alxgmpr/moisture-sensor/docs/footprint-standardization-2026-09-09/README.md

# Standard KiCad footprints — 9 September 2026

Implemented the requested corrections in the maintained PCB and schematic.

- All 11 resistors use `Resistor_SMD:R_0402_1005Metric`.
- Nine 0402 capacitors use `Capacitor_SMD:C_0402_1005Metric`; C3 retains the standard 0603 pattern.
- Corrected C21/C22/C23/C24/C27 pad rotation by loading standard library geometry. Replaced C26 and R22/R23/R36/R37 hand-solder geometry with standard reflow geometry and moved 12 attached track endpoints to the new pad centers.
- D1–D10 now use `Package_SON:Texas_DPY0002A_0.6x1mm_P0.65mm`. Its pad dimensions and centers match the former custom pattern. The installed library's referenced STEP model is missing, so the existing local matching DPY model is retained; copper, mask, paste, courtyard, silk and fabrication geometry come from KiCad.
- Other ICs already select standard KiCad footprints. Retained the verified custom module, battery holder, crystal and inductor patterns because matching part-specific entries were not found in the installed standard library.
- Preserved every footprint placement, purchased part number, pad-to-net assignment, via, and keepout. The user confirmed the no-via corridor is intended for GND vias only; the two existing +3V3 keepout errors are accepted for this change. Rules and exclusions were not edited.
- Updated HARDWARE.md and LAYOUT.md to the selected Lian Xin CR2032-BS-6/C22363833 holder, corrected C22/C24 to 0402 X7R/50 V, and corrected the holder-model entry in NEXT-STEPS.md.
- Regenerated [product-bom.csv](product-bom.csv) using KiCad's schematic exporter, then regenerated the BOM.md table from that CSV. Purchasing MPNs are unchanged.

## Validation

[Geometry and preservation checks](verification.json) confirm all 31 updated footprints have the standard library's pad numbers, positions, orientation, size, shape, corner ratio and copper/mask/paste layers. No HandSolder footprint remains in the maintained PCB or schematic.

[Final DRC](drc.json): zero unconnected items, zero schematic parity differences, and only the two user-accepted +3V3 keepout errors. There are 39 warnings: 35 silk/text, two existing IC-library differences, one dangling track and one dangling via. Some silk overlaps result from retaining unmodified standard footprint silk. No additional electrical DRC error was introduced.

[ERC](erc.json): zero errors and 11 warnings (ten symbol/library differences and one connected no-connect warning).

[Full existing test suite](tests.txt): 49 tests, 46 pass, three fail. Re-running the suite with PCB/schematic/project reads redirected to the saved pre-change files reproduces the same three failures; [baseline comparison](baseline-tests.txt). The failures concern the outdated model-less test-point inventory, a D8 ground-via proximity expectation, and the existing SENSE track-width setting. No new test failure remains. The subprocess-based export checks use the maintained schematic in both runs; the three failing tests read the snapshotted source directly.

Inspected the updated [top view](top.png), component closeups, and KiCad layer exports in [layers](layers/). Available models show no new obvious component collision. The new standard pads remain connected after zone refill and trace-end adjustment.

The [preceding review](../footprint-review-2026-09-09/README.md) records the pre-change findings. Its recommendation concerning the two +3V3 vias is superseded by the user's explicit clarification above. Existing fabrication ZIPs/Gerbers were not regenerated by this footprint update; generate production output from the corrected sources before ordering.
