alxgmpr/moisture-sensor/output/front-graphic-concepts/prompts-botanical.md

# Botanical variants

Created with the built-in image generator, editing mono-v2.png.

## sunflower

Edit the supplied black-and-white pixel-art plant emblem. Preserve the existing pot, bottom two leaves, curved stem base, three radio wave arcs at upper right, black and white palette, square canvas, and overall scale. Replace ONLY the carnivorous head and its upper attachment with the requested non-carnivorous plant top. No teeth, jaws, mouth, eyes, face, spikes or carnivorous features. A charming botanical radio-broadcasting emblem, waves visually radiate from the new plant top. Bold crisp stair-stepped square pixel edges, simple chunky shapes, high readability on a small device. Solid black and pure white only. No gray, textures, shading, text, additional objects or borders. Replace head with a single round sunflower with a bold black central disk, small white center detail, and a ring of about eight broad blocky petals separated by white notches. Flower tilts subtly toward the radio arcs. Keep flower compact and silhouette unmistakable.

## sprout

Edit the supplied black-and-white pixel-art plant emblem. Preserve the existing pot, bottom two leaves, curved stem base, three radio wave arcs at upper right, black and white palette, square canvas, and overall scale. Replace ONLY the carnivorous head and its upper attachment with the requested non-carnivorous plant top. No teeth, jaws, mouth, eyes, face, spikes or carnivorous features. A charming botanical radio-broadcasting emblem, waves visually radiate from the new plant top. Bold crisp stair-stepped square pixel edges, simple chunky shapes, high readability on a small device. Solid black and pure white only. No gray, textures, shading, text, additional objects or borders. Replace head with a botanical leafy shoot: upper curved stem ending in three broad smooth oval pixel leaves, one top leaf and two alternating side leaves, each with a simple white central vein. Healthy ordinary houseplant, no flower, no face. Leaves cluster in the old head area beside the waves.

## tulip

Edit the supplied black-and-white pixel-art plant emblem. Preserve the existing pot, bottom two leaves, curved stem base, three radio wave arcs at upper right, black and white palette, square canvas, and overall scale. Replace ONLY the carnivorous head and its upper attachment with the requested non-carnivorous plant top. No teeth, jaws, mouth, eyes, face, spikes or carnivorous features. A charming botanical radio-broadcasting emblem, waves visually radiate from the new plant top. Bold crisp stair-stepped square pixel edges, simple chunky shapes, high readability on a small device. Solid black and pure white only. No gray, textures, shading, text, additional objects or borders. Replace head with a single upright tulip blossom: simple broad black cup with three rounded stair-step petal tips, two short white inset seams suggesting overlapping petals. Slight lean toward radio waves. Graceful compact tulip silhouette.
