alxgmpr/moisture-sensor/output/front-graphic-concepts/prompts.md

# Radio flytrap graphic concepts

Generated using the built-in image generation tool. Concept previews; not yet sized or prepared for manufacturing.

## classic

Create one original pixel art emblem for the front of a wireless soil moisture sensor. An original cheerful Venus flytrap mascot broadcasting radio waves out of its open jaws. Design distinctly as a botanical Venus flytrap: two elongated hinged leaf jaws edged with little cilia, not a round spotted flower head; grows from a small terracotta flowerpot, no pipe. Two small leaves on its stem. Mouth faces up-right. Exactly three separated expanding radio-wave arcs originate just outside the mouth, shaped from crisp stair-stepped square pixels. Compact balanced composition, full subject visible with generous blank margins. Authentic low-resolution sprite, consistent square pixel grid, nearest-neighbor hard edges, limited flat colors, no smooth vector curves, blur, gradients, text, watermark, scenery, border, or device mockup. Plain ivory background. Very chunky 8-bit sprite. Lime green leaf jaws with coral interior, dark green stem and two leaves, orange terracotta flowerpot, electric cyan radio waves. Dark charcoal pixel outlines. Simple and cheeky expressive pose, roughly 48x48 logical pixel design.

## forest

Create one original pixel art emblem for the front of a wireless soil moisture sensor. An original cheerful Venus flytrap mascot broadcasting radio waves out of its open jaws. Design distinctly as a botanical Venus flytrap: two elongated hinged leaf jaws edged with little cilia, not a round spotted flower head; grows from a small terracotta flowerpot, no pipe. Two small leaves on its stem. Mouth faces up-right. Exactly three separated expanding radio-wave arcs originate just outside the mouth, shaped from crisp stair-stepped square pixels. Compact balanced composition, full subject visible with generous blank margins. Authentic low-resolution sprite, consistent square pixel grid, nearest-neighbor hard edges, limited flat colors, no smooth vector curves, blur, gradients, text, watermark, scenery, border, or device mockup. Plain ivory background. Rich 16-bit fantasy woodland sprite. Long elegant curving moss-green stem, emerald toothed leaf jaws with plum-purple interior, warm clay flowerpot, golden radio waves. Roughly 64x64 logical pixels with restrained flat pixel shading, no more than 9 colors. Charming lively upward broadcasting pose.

## mono

Create one original pixel art emblem for the front of a wireless soil moisture sensor. An original cheerful Venus flytrap mascot broadcasting radio waves out of its open jaws. Design distinctly as a botanical Venus flytrap: two elongated hinged leaf jaws edged with little cilia, not a round spotted flower head; grows from a small terracotta flowerpot, no pipe. Two small leaves on its stem. Mouth faces up-right. Exactly three separated expanding radio-wave arcs originate just outside the mouth, shaped from crisp stair-stepped square pixels. Compact balanced composition, full subject visible with generous blank margins. Authentic low-resolution sprite, consistent square pixel grid, nearest-neighbor hard edges, limited flat colors, no smooth vector curves, blur, gradients, text, watermark, scenery, border, or device mockup. Plain ivory background. Minimal one-color black pixel stamp on pure white. Bold black hinged leaf jaws, white negative-space mouth, thick curved stem, two leaves, simple tapered flowerpot, three bold separated stair-stepped radio arcs. Roughly 40x40 logical pixel design. Large sturdy pixel features and generous negative spaces for a tiny front-face print. No gray.
