alxgmpr/moisture-sensor/firmware/BL54L15-port.md

# BL54L15 sensor firmware port

A real sensor qualification image is now available in [sensor](sensor/README.md), built against nRF Connect SDK 3.2.2 with the sensor overlay. Existing DK applications retain their bench targets. The remaining requirements below still need physical qualification; no sensor has been built or measured.

## GPIO and programming

Main bus: SCL=P1.11 (module35), SDA=P1.10 (28). Dedicated FDC bus:
SDA=P1.05 (22), SCL=P1.04 (23), on TWIM20 with switched pull-ups.

PMIC_INT=P0.00 (17), SWO=P2.07 (4). Dedicated SWDIO/SWDCLK/nRESET are module5/6/7.
J4 and its reset connection to nPM2100 PG/RESET are unchanged. The module ships
without application firmware; program through J4. P1.00/P1.01 are reserved
for XL1/XL2; never enable them as digital outputs while X1 is fitted. Unused
module pins are NC in the schematic; disconnect unused input buffers in sleep.

## Crystal configuration

X1 remains CM8V-T1A, 32.768 kHz, **CL=7 pF**, ±20 ppm. Its terminals connect
only to module25 XL1 and module24 XL2. There are no discrete load capacitors.
Use internal load banks and the device-specific FICR calibration through the
SDK oscillator driver before LFXO startup.

**Corrected from the old hardware notes:** CL is the crystal's total load across
its terminals. The current Nordic devicetree guidance says
`load-capacitance-femtofarad` selects the internal capacitor, not CL directly.
For equal legs, use `CL ≈ (CINT + Cadditional_per_leg)/2`, where additional
loading includes host/module traces and pin loading not already represented by
the trimmed bank. Do not count the same calibrated pin loading twice. Thus 7 pF
CL needs approximately 14 pF per leg before subtracting those parasitics.

An initial engineering estimate of 2 pF additional loading per leg gives
**CINT≈12 pF**; 1–3 pF would imply 13–11 pF. Start from a supported setting near
12,000 fF and tune on the assembled board. This is an explicit parasitic
assumption, not a measured or vendor-certified trim. Neither 7,000 fF copied
from CL nor the Ezurio DVK's 15,500 fF should be inherited without calculation.
Verify the selected SDK's binding/driver and generated secure-image devicetree;
then measure frequency, cold/low-voltage startup, drive margin and temperature
behavior using a buffered clock output or appropriate low-loading technique.
Do not probe crystal pins with an ordinary oscilloscope probe.

Example sensor starting point (not applied to DK applications):

```dts
&lfxo {
    load-capacitors = "internal";
    load-capacitance-femtofarad = <12000>; /* Initial estimate; trim on sensor. */
    status = "okay";
};

&hfxo {
    load-capacitors = "internal";
    load-capacitance-femtofarad = <15000>; /* BL54L15 DVK module starting value. */
    status = "okay";
};
```

The module contains its own 32 MHz crystal, with the load banks inside the SoC.
The 15,000 fF HFXO starting value follows the upstream Ezurio BL54L15 DVK board
configuration for this module; it is not the old bare-board X2 CL=8 pF value.
Verify HFXO startup and frequency with the intended SDK and module revision.
Enable the SoC's main DC/DC regulator using that SDK's regulator binding; the
inductor and rail support are in the module, so no host DCC wiring is needed.

Select LFXO as LFCLK and retain the System OFF/GRTC timed-wake design. Wait for
clock startup, configure/retain the required low-frequency/GRTC domain, arm the
wake deadline, and test repeated timed System OFF cycles at voltage and
temperature limits. A DK wake test alone does not verify the new sensor layout.

## nPM2100 and radio

Keep 3.3 V VOUT and the existing FDC load-switch/I²C sequencing. Extend the
existing force-HP measurement window to cover **every radio TX/RX window** and
its settling time. LP/ULP has about 70 mVpp typical ripple; Ezurio permits at most
10 mV supply ripple/noise for undisturbed radio operation. HP is a mitigation,
not a guaranteed 10 mV specification. Measure at module26 with a short ground
spring over relevant bandwidth, including startup, transitions and depleted-
cell bursts. Revisit filtering if it fails; account for the module input
capacitance in nPM2100's effective VOUT-capacitance limit. Recalculate the battery
budget from measured module and converter current. Never switch off VOUT while
relying on SoC System OFF/GRTC wake.

## Sources (accessed 2026-09-04)

- [Ezurio module datasheet](https://www.ezurio.com/documentation/datasheet-bl54l10-and-bl54l15-series), Clocks, Circuit Checklist, Pin-Out and operating conditions.
- [Nordic LFXO internal capacitor model](https://docs.nordicsemi.com/r/bundle/ngl_001/page/gl/ngl_001/lfxo_internal_capacitor.html) and [LFXO devicetree](https://docs.nordicsemi.com/r/bundle/ngl_001/page/gl/ngl_001/lfxo_devicetree.html).
- [Zephyr nRF54L LFXO binding](https://docs.zephyrproject.org/latest/build/dts/api/bindings/clock/nordic,nrf54l-lfxo.html) and [factory-trim implementation](https://github.com/zephyrproject-rtos/zephyr/blob/main/soc/nordic/nrf54l/soc.c).
- [Ezurio BL54L15 DVK clock/regulator configuration](https://github.com/zephyrproject-rtos/zephyr/blob/main/boards/ezurio/bl54l15_dvk/nrf54l_10_15_cpuapp_common.dtsi). This is a module reference, not a sensor pin assignment.
- Local Nordic nPM2100 Datasheet v1.0, boost operating modes and external component limits.

## Timing-marker pads

The sensor now exposes **MARK1 / TP16 on P1.07 (U1 pad 20)** and **MARK2 / TP17 on P1.06 (U1 pad 21)**. For Zephyr these are `gpio1` pins 7 and 6. Reserve both for optional instrumentation; hardware routing alone does not enable output toggling. P0.01/P0.02 remain unused. [Board map](../docs/testpoints-2026-09-07/README.md).
