alxgmpr/moisture-sensor/docs/sweep-2026-09-09.md

# Development checkpoint — 2026-09-09

User requested a sweep commit before planning capacitor and diode consolidation.
This checkpoint captures the accumulated board, schematic, rules, procurement,
review, bring-up firmware, simulation, and export-tool work as it stands.
It is a development snapshot, not a newly verified fabrication release.

## Verification at checkpoint

`python3 -m unittest discover -s tests`: 51 tests ran, 48 passed, 3 failed:

- `test_only_bare_copper_footprints_are_model_less`: expected model-less references
  still include removed fiducials and omit added testpoints/tooling holes.
- `test_probe_clamps_have_nearby_ground_vias_in_ground_plane`: D8 has no qualifying
  ground-plane via within the test's 0.7 mm radius. Investigate current copper and
  the intended return path before deciding whether layout or expectation changes.
- `test_routing_classes_use_production_safe_dimensions`: SENSE clearance is
  0.6 mm in the project versus 0.2 mm in the test expectation.

`git diff --check` reported six whitespace-only lines in the maintained schematic.
They are preserved in this snapshot. No ERC/DRC release claim is made by this commit.

## Repository scope

Scratch files in `tmp`, the EasyEDA cache, and generated `output` media remain
local and are ignored. Output Python/shell source and Markdown notes are tracked
explicitly. Dated review artifacts under `docs` are retained with their evidence.
No files were deleted and no hardware or BOM substitutions were made for this checkpoint.

The next change records the proposed consolidated development BOM and the quoted
cost model. Capacitor selection/layout work and diode implementation follow that plan.
