alxgmpr/moisture-sensor/docs/audit-2026-07-31.md

# Layout and netlist audit — 2026-07-31

Read-only pass against commit `68ed8a2`. No files were modified.

Evidence sources:

| Source | Used for |
|---|---|
| `doc/nRF54L15_qfaa_4L_config1_schematic.pdf` | nRF54L15 support topology and values (Nordic, rev v0.8, 04.02.2025) |
| `doc/nRF54L15_qfaa_4L_config1_pcb.pdf` | nRF54L15 reference placement |
| `docs.nordicsemi.com` nPM1300 PS | QFN32 pin assignment, BUCK reference circuitry |
| `doc/datasheets/FDC1004.pdf` (TI, 2.9 MB) | downloaded |
| `doc/datasheets/TPS7A1650.pdf` (TI, 1.6 MB) | downloaded |
| `doc/datasheets/SHT4x.pdf` (Sensirion, 0.9 MB) | downloaded |
| `kicad-cli 10.0.5` netlist / ERC / DRC | connectivity and rule checks |

DigiKey API was not used — the credentials file is read-blocked in this
environment and `requests` is not installed. Datasheets came from the
manufacturer URLs already stored in the schematic's `Datasheet` properties,
which is equivalent for these four parts.

---

## Summary

| # | Finding | Severity |
|---|---|---|
| 1 | `/VSET1` track shorts to the GND pour — 2 DRC clearance errors at 0.0000 mm | Error |
| 2 | `SENSE1`/`SENSE2`/`SHLD` electrode zones are isolated copper — no connection to U3 | Error |
| 3 | BUCK1 is unused but VSET1/R21 is populated and routed | Design question |
| 4 | Bypass caps sit 2.5–9.6 mm from the pins they serve | Layout |
| 5 | Ground returns up to 4.87 mm from the nearest ground via | Layout |
| 6 | L10 oriented backwards — switch node runs 4.69 mm; BUCK2 loop 5.50 mm² | Layout |
| 7 | Crystal routing asymmetric — 1.41 mm mismatch on XC1/XC2 | Layout |
| 8 | 42 of 146 track segments off a 45° multiple | Geometry |
| 9 | Schematic: 115/115 symbols unrotated, 0 junctions, no `+3V3` power symbol | Drawing |
| 10 | 8 `PWR_FLAG`s suppress ERC power checks | Drawing |
| 11 | J1 footprint does not match its library copy | DFM |
| 12 | NEXT-STEPS.md §1 claims "0 DRC errors" — currently 9 | Stale doc |

DRC totals: **9 violations (2 errors, 7 warnings), 44 unconnected pads.**
ERC: 0 violations.

---

## 1. `/VSET1` shorts to the ground pour — Error

Two F.Cu segments on `/VSET1` sit at 0.0000 mm from `ZoneB_GND_F`, against a
0.1270 mm rule:

```
@(72.1000, 97.9243)  Track [/VSET1] on F.Cu, length 0.2465 mm
@(72.1000, 100.0025) Track [/VSET1] on F.Cu, length 2.0782 mm
```

`/VSET1` is `R21.1 + U2.17`, and R21's other end is already on GND.

**Root cause — corrected, and it was not a routing error.** The offending
copper is a **ground stitching via**, `(71.50, 100.00)` in the `STITCH` list in
`tools_route.py`. R21 is rotated −90°, which puts its VSET1 pad at:

```
R21 pad 1 (VSET1)   x span 71.7800 .. 72.4200
stitch via 0.60 mm  x span 71.2000 .. 71.8000
                              overlap 0.02 mm
```

A 0.02 mm overlap between a GND via and a VSET1 pad. KiCad merged them, which
is why DRC reported it as a VSET1 *track* at zero clearance to the pour — the
symptom pointed at the routing, the cause was in the stitching array.

**Fixed** — the via moved to `(70.90, 100.00)`, which holds 0.58 mm to R21's
pad and 1.09 mm to C25's. R21 and the `/VSET1` net are unchanged; nothing
needed deleting, so finding 3 below is a documentation question, not a fix.

This is worth remembering as a class: a stitching array is generated from a
coordinate list that knows nothing about what is placed, so moving or rotating
any part can put a pad under a via, and the violation surfaces against the
*net that got merged*, not against the via.

## 2. Sense electrodes are isolated copper — Error

Four `isolated_copper` warnings:

```
@(69.0, 159.0)  Zone 'SENSE1_electrode'    [/SENSE1] F.Cu
@(69.0, 122.0)  Zone 'SENSE2_electrode'    [/SENSE2] F.Cu
@(67.3, 112.0)  Zone 'ZoneC_GUARD'         [/SHLD]   B.Cu, In2.Cu  (x2)
@(67.0, 105.8)  Zone 'SenseEscape_GUARD'   [/SHLD]   B.Cu, In2.Cu  (x2)
```

The zones carry the correct nets — `SENSE1_electrode`→`/SENSE1`,
`SENSE2_electrode`→`/SENSE2`, both guard zones→`/SHLD`. What is missing is
copper joining each zone to U3's pins: `/SENSE1` (U3.2 CIN1), `/SENSE2`
(U3.3 CIN2) and `/SHLD` (U3.1 SHLD1, U3.6 SHLD2) have no track anywhere on
the board. These three nets are the entire measurement function.

## 3. BUCK1 unused but VSET1 populated — Design question

nPM1300 BUCK1 is not used:

| Pin | Name | State |
|---|---|---|
| 1 | VOUT1 | no-connect |
| 3 | SW1 | no-connect |
| 2 | PVSS1 | GND |
| 17 | VSET1 | R21 → GND |

Only BUCK2 is built out (SW2→L10→VOUT2 = `/+3V3`). With BUCK1 disabled, R21
and the `/VSET1` net configure a regulator that never runs — and that net is
the one shorting to the pour in finding 1. Either drop R21 and `/VSET1`, or
record why the strap is needed. Same question applies to LOADSW2/LDO2
(pins 30, 31 both no-connect) though those have no external parts attached.

## 4. Bypass capacitor distances — Layout — **DECA bank and C3 fixed**

> **Resolved for the DECA bank.** C2, C12 and C5 all had their `/DECA` pad on
> the WEST side, pointing away from U1, so the net left each capacitor going
> the wrong way and doubled back — 1.13 mm each, recovered by a rotation. With
> the furthest legal eastward shift on top:
>
> | | was | now |
> |---|---|---|
> | C2 → U1.43 | 8.17 mm | **6.04 mm** |
> | C12 → U1.43 | 8.19 mm | **6.59 mm** |
> | C5 → U1.43 | 8.44 mm | **6.90 mm** |
>
> The shift is small because the band between the bank and the FB1/L1 column
> is 0.67 mm; each cap moved until its courtyard met its neighbour, leaving
> 0.20 mm. The remaining ~6 mm is a packaging consequence and not a nudge:
> a 0402 hand-solder courtyard is 2.28 mm on its long axis and the corridor
> between the L1/FB1 column and U1 is 1.50 mm, so **no orientation of a 0402
> fits there at all**. Nordic gets these against the pins because their
> reference uses 0201s. Closing it means 0201s for this bank or re-planning the
> whole west side of U1.
>
> **C3 too**, same cause: its `+3V3` pad was on the west side at x = 65.138
> while U1.48 is at 74.079, so the rail left the bulk cap heading away from the
> part it feeds. A 0603's pads are further apart, so the rotation is worth more
> — 1.72 mm — and east is capped at centre 66.97 by C10's courtyard on one row
> and X1's on the other. **9.43 mm → 6.93 mm.**
>
> Turning C3 also moved its feed: running west from the new pad crosses C3's
> own ground pad, which DRC reported as a `+3V3`/GND short. Its via moved to
> the south side.

Distance from each cap's signal pad to the nearest same-net IC pin:

| Cap | Net | Serves | Distance |
|---|---|---|---|
| C3 | +3V3 | U1.48 VDD | **9.43 mm** |
| C27 | +3V3 | U4.3 VDD (SHT45) | **9.58 mm** |
| C5 | DECA | U1.43 | **8.44 mm** |
| C12 | DECA | U1.43 | **8.19 mm** |
| C2 | DECA | U1.43 | **8.17 mm** |
| C26 | +3V3_FDC_SW | U3.8 VDD | **6.43 mm** |
| C24 | +3V3 | U2.32 VOUT2 | **5.75 mm** |
| C1 | DECD | U1.45 | **5.18 mm** |
| C10 | +3V3 | U1.48 VDD | **5.14 mm** |
| C21 | VSYS | U2.20 | 5.24 mm |
| C13 | NRESET | U1.30 | 5.25 mm |
| C4 | +3V3 | U1.36 VDD | 3.38 mm |
| C23 | VBAT | U2.19 | 3.16 mm |
| C22 | VSYS | U2.20 | 3.16 mm |
| C30 | SOLAR_PANEL | U5.8 IN | 2.72 mm |
| C8 | +3V3 | U1.10 VDD | 2.69 mm |
| C31 | SOLAR_5V | U5.1 OUT | 2.62 mm |
| C7 | +3V3 | U1.22 VDD | 2.48 mm |
| C20 | VBUS_IN | U2.21 VBUS | 2.34 mm |
| C6 | RF_PA_RETURN_LOCAL | U1.32 VSS_PA | 2.28 mm |
| C25 | +3V3 | U2.12 VDDIO | 1.61 mm |

For comparison, Nordic's reference layout (`nRF54L15_qfaa_4L_config1_pcb.pdf`)
places C2, C12 and C5 directly against the DECA/DECRF pins, and C3/C10/L1/FB1
tight against the package corner — everything within roughly 1–2 mm. The
three DECA caps here are at 8.2 mm.

C1 at 5.18 mm from DECD matters more than its position in the list suggests:
DECD is the DC/DC output node and carries the switching ripple.

C27 at 9.58 mm from the SHT45's VDD is a separate case — U4 sits on the
jut-out at board (39.8, 20.6) while C27 is at (31.5, 20.6), so the bypass is
on the far side of the enclosure wall from the part it decouples.

**Attempted and reverted.** The distance is structural, not an oversight.
Three rule areas govern the tab: `SHT45_Jut` bans pour and vias across all of
it, `NoCopperSHT45` bans tracks as well under the die. So both rails must come
around U4 from the east, and exactly one strip could carry a bridging cap:

| | width |
|---|---|
| east strip, x 101.045–102.000 | 0.955 mm |
| 0402 rotated | 1.010 mm — does not fit |
| 0201 rotated | 0.790 mm — fits |

A 0201 was swapped in and placed at (101.47, 60.60) rot 90, inside a 0.06 mm
window bounded by U4's courtyard on one side and the 0.300 mm board-edge
clearance on the other. **The placement is legal; the routing is not.** The two
hops onto its pads kept merging with the long tab runs and dragging `+3V3` back
across U4's pads and into the die keepout — 10 DRC violations including a
`+3V3`/`/SCL` short. Reverted to the known-good state.

It is also the weakest electrical case on the board. The SHT45 is an I²C part
at 400 kHz drawing microamps idle and ~60 mA only while its heater fires, on
millisecond timescales; ~10 nH of loop is immaterial there. Contrast C9, where
5 nH flipped a 2.4 GHz shunt inductive.

To close it later: place the 0201 at (101.47, 60.60) rot 90 and draw the two
0.3 mm hops **by hand**, keeping both east of x = 101.2 so neither crosses
`NoCopperSHT45`.

**Root cause worth noting:** every support passive is a 0402 HandSolder
footprint where Nordic's reference uses 0201. The larger pads and the
elongated hand-solder geometry are part of why the caps cannot sit as close.
That is an assembly choice, not an error, but it caps how much of this gap is
recoverable.

## 4a. C9's shunt branch was inductive — **FIXED**

Not in the original audit; found by re-reading Nordic's reference against our
stackup. Nordic's rule 2 is that C9's ground must reach *only* the bottom
ground layer, isolated from the rest. The isolation was implemented correctly —
the via is on `/RF_C9_RETURN_BOTTOM`, so `ZoneB_GND` on In1.Cu clears it — but **there was
no bottom ground layer to land on.**

Nordic's config-1 4-layer has ground on L2, L3 **and** L4 (visible on pages 3–5
of `nRF54L15_qfaa_4L_config1_pcb.pdf`: two solid inner ground planes and a
poured bottom). Ours has ground on In1.Cu only — In2.Cu is the 3V3 plane and
B.Cu in Zone B was bare. So the return ran ~5 mm as a narrow B.Cu track to the
nearest stitching via, and a narrow track is an inductor:

| leg | mm | nH |
|---|---|---|
| F.Cu stub to the via | 0.83 | 0.50 |
| through via F.Cu→B.Cu | 1.49 | 1.34 |
| B.Cu via → NT2 | 1.30 | 0.52 |
| B.Cu NT2 → stitch via | 4.20 | 1.68 |
| via B.Cu → In1.Cu | 1.27 | 1.15 |
| **total** | | **5.18** |

At 2.4 GHz that is **+j78.2 Ω** against C9's own −j33.2 Ω, so the shunt branch
came out at **+45 Ω — inductive**. A 2.0 pF shunt capacitor behaving as an
inductor. Exactly the failure the C6 stub had, one layer down.

**Fixed** by adding `ZoneB_GND_B`, a B.Cu ground pour local to the RF return
(x 78.0–88.0, y 51.5–62.0), so the via lands in copper that spreads instead of
a track that doesn't. Path is now stub + via + a short hop: **2.04 nH,
+j30.7 Ω, branch −2.5 Ω and still capacitive.** The 4.20 mm detour is deleted.

The pour starts 1.20 mm east of the `/ANT` column at x = 76.80, so it never
sits under the RF trace and the 50 Ω microstrip-over-In1.Cu geometry from
LAYOUT.md §2 is untouched. Three existing stitching vias — (81.50, 55.00),
(84.00, 55.00), (86.50, 55.00) — tie it to In1.Cu, all ≥ 4.70 mm from the trace.

**Worth checking on the VNA at bring-up** along with the rest of the matching
network; the inductance figures are estimates at 0.4–0.9 nH/mm, not extractions.

## 5. Ground return distances — Layout — **FIXED**

> **Resolved.** The stitching array is a 2.5 mm grid that knows nothing about
> where the decoupling landed, so four caps were returning through whatever via
> happened to be nearby. Four vias placed against the ground pads instead:
>
> | | was | now |
> |---|---|---|
> | C1 (DECD output, carries the ripple) | 4.87 mm | **1.13 mm** |
> | C2 | 2.64 mm | **0.93 mm** |
> | C12 | 2.60 mm | **1.31 mm** |
> | C5 | 2.44 mm | **1.31 mm** |
>
> C1 was the longest leg of the nRF54L15 DC/DC loop by a wide margin.

Distance from each cap's ground pad to the nearest ground via. Return current
goes through the plane, so this is the meaningful figure rather than lateral
distance to a VSS pin.

| Cap | To nearest GND via |
|---|---|
| C1 | **4.87 mm** |
| C13 | **4.62 mm** |
| C10 | **4.31 mm** |
| C30 | 3.68 mm |
| C7 | 3.41 mm |
| C20 / C22 / C23 | 3.29 mm |
| C12 | 3.23 mm |
| C5 | 3.09 mm |
| C31 | 2.80 mm |
| C2 | 2.66 mm |
| C27 | 1.94 mm |
| C8 / C3 / C4 | 1.81–1.85 mm |
| C21 | 1.63 mm |
| C26 | 1.52 mm |
| C25 | 1.35 mm |
| C11 | 0.90 mm |

C1 again is the one to fix first — it is the DC/DC output cap, so both its
signal side (5.18 mm) and its return (4.87 mm) are long.

## 6. BUCK2 switching loop — Layout

Measured from pad geometry, board coordinates:

```
U2.5  SW2    ( 7.074, 56.250)
L10.1        ( 3.275, 53.500)   <- SW2 side, FAR pad
L10.2        ( 4.725, 53.500)   <- VOUT2 side, near pad
C24.1 +3V3   ( 3.138, 57.000)
C24.2 PVSS2  ( 4.862, 57.000)
U2.6  PVSS2  ( 7.074, 56.750)

enclosed area  : 10.03 mm²  (convex hull)
loop perimeter : 14.43 mm
```

> **Correction.** The first version of this finding gave the enclosed area as
> 5.50 mm². That figure was wrong. As placed, the pad sequence self-intersects
> — the path runs x = 3.275 → 4.725 → 3.138, doubling back on itself — and the
> shoelace formula cancels signed area across a bowtie, understating it. The
> real enclosed area is 10.03 mm², and it is the same before and after the
> rotation below, because the four corners of the loop do not move.
> `tools_loop_area.py` now refuses to report a shoelace figure for a
> self-intersecting path.

**L10 is oriented backwards.** `/SW2` connects U2.5 to L10.1, which is the pad
*further* from U2 — so the highest-dv/dt net on the board runs the length of
the inductor body to reach its own pad. Rotating L10 180° shortens both halves:

| | As placed | Rotated 180° |
|---|---|---|
| SW2 run (U2.5 → L10 pad 1) | 4.69 mm | **3.62 mm** |
| VOUT run (L10 pad 2 → C24.1) | 3.84 mm | **3.50 mm** |
| Enclosed area | 10.03 mm² | 10.03 mm² |

There is no trade — both runs improve — but note what it does and does not buy:
it takes 1.07 mm off the switching node, and it does **not** reduce the loop
area. Shrinking the loop needs L10 and C24 moved closer to U2, which is a
placement change, not an orientation one.

`/SW2` has no copper at all, so this costs nothing to do now.

### nRF54L15 DC/DC loop

Measured the same way, and it self-intersects too (shoelace 4.38, hull 7.77):

```
U1.46 DCC    (14.079, 24.400)     run U1.46 -> L1.1   3.20 mm
L1.1         (10.875, 24.400)     run L1.1  -> L1.2   1.75 mm
L1.2         ( 9.125, 24.400)     run L1.2  -> C1.1   1.92 mm
C1.1  DECD   ( 9.433, 26.300)     run C1.1  -> C1.2   1.13 mm
C1.2  GND    (10.567, 26.300)     run C1.2  -> U1.44  4.43 mm
U1.44 VSS    (14.079, 23.600)

enclosed area : 7.77 mm² (hull)
```

L1 is already turned the right way — `tools_place_fixups.py` records that fix
and the reasoning. What is left is the **return**: C1's ground pad is 4.43 mm
from U1's VSS pin and 4.87 mm from the nearest ground via, which is the longest
leg of the loop by a wide margin. Pulling C1 in is the change that matters
here, not another rotation.

### TPS7A1650

Checked for the same thing and it does not apply — an LDO has no switching
loop. Its cap distances (C30 2.72 mm to IN, C31 2.62 mm to OUT) are in the
table above and are much less critical at 100 mA.

## 7. Crystal routing — Layout

| Net | Pads | Direct span | Routed copper | Overshoot |
|---|---|---|---|---|
| XC1 | U1.34 ↔ X2.1 | 5.12 mm | **7.09 mm** | +38% |
| XC2 | U1.35 ↔ X2.3 | 3.76 mm | **5.68 mm** | +51% |
| XL1 | U1.1 ↔ X1.1 | 5.79 mm | 6.75 mm | +17% |
| XL2 | U1.2 ↔ X1.2 | 4.97 mm | 5.52 mm | +11% |

Two problems. The routed lengths are mismatched — **1.41 mm between XC1 and
XC2** on the 32 MHz oscillator and 1.23 mm between XL1 and XL2 — which
unbalances the load presented to each side of the crystal. And both pairs are
long: Nordic's reference places X2 immediately adjacent to XC1/XC2.

Neither crystal has external load capacitors, which matches Nordic's reference
(both use the internal caps) and HARDWARE.md's crystal section. Not a finding.

## 8. Track angles — Geometry — **FIXED**

> **Resolved.** All 192 segments now lie on 0/45/90/135°.
> `tools_lint_angles.py` passes, and `tools_route.py` can no longer emit an
> off-angle segment: waypoint pairs that are neither axial nor diagonal are
> decomposed at emit time, and `check_angles()` aborts the run if anything
> survives. DRC stayed at 1 violation (the J1 library warning) and the netlist
> is unchanged.
>
> The decomposition needed a corner-selection rule. Inserting a corner
> mechanically moved copper inside the tight escapes and took DRC from 1 to 8;
> a fixed preference for either corner gave 7 whichever way round. Choosing
> whichever corner keeps furthest from other nets' pads got it to 6, and the
> last five were routes whose waypoints had to be rewritten to be natively
> on-grid — `/XC1`, `/DECA`, `/DECD` and `/NRESET`, all in U1's escape
> corridor, plus the `/SW2` and `L10 → C24` pair fixed earlier.
>
> Most of the original 42 were not deliberate diagonals. They came from a
> waypoint written to two decimals against a pad sitting at three: a pad at
> y = 60.079 with the next waypoint at 60.05 reads as horizontal and is 1.33°.
> Several were under a tenth of a degree — invisible in the editor, and
> perfectly visible to a fab.

The state that prompted this, for the record — 42 of 146 segments off a 45°
multiple (29%):

| Bucket | Count |
|---|---|
| 0° | 46 |
| 90° | 51 |
| 45° | 4 |
| 180° | 3 |
| **off-angle** | **42** |

By layer: F.Cu 38, B.Cu 4.
By net: `/+3V3` 10, `/DECA` 7, `/DECD` 6, `/NRESET` 4, `/PMIC_INT` 3,
`/RF_PA_RETURN_LOCAL` 2, `/XL1` 2, `/XL2` 2, `/RF_C9_RETURN_BOTTOM` 2, and one each on `/RF_FILTER_N1`,
`/XC1`, `/SWD_RST`, `/SWDCLK`.

Longest offenders:

| Net | Angle | Length | Layer |
|---|---|---|---|
| `/XC1` | 3.38° | 5.08 mm | F.Cu |
| `/XL1` | 155.22° | 2.86 mm | F.Cu |
| `/PMIC_INT` | 78.69° | 2.55 mm | B.Cu |
| `/XL2` | 146.98° | 2.39 mm | F.Cu |
| `/+3V3` | 158.96° | 1.67 mm | F.Cu |

The crystal nets appear in both this list and finding 7.

## 9–10. Schematic drawing — Drawing

| Property | Value |
|---|---|
| Symbol instances at rotation 0 | 115 of 115 |
| Junctions | 0 |
| Net labels | 146 (`+3V3` alone appears 21× as plain text) |
| `power:+3V3` symbols | 0 |
| `power:GND` symbols | 47 |
| `PWR_FLAG` | 8 |
| Sheets | 1 flat, extent 513 × 325 mm |

ERC reports 0 violations, but with 8 `PWR_FLAG`s in place the power-driving
checks are largely inert. The `+3V3` rail in particular has no power symbol at
all, so it is not being checked as a rail.

Annotation is clean — 115 unique references, none unannotated, no duplicates.
`kicad-cli` emits "schematic has annotation errors" during netlist export;
that warning does not reproduce under ERC and appears spurious.

## 11. J1 footprint mismatch — DFM

```
[lib_footprint_mismatch] Footprint 'USB_C_Receptacle_HRO_TYPE-C-31-M-12'
does not match copy in library 'Connector_USB'   @(63.5, 85.5)  J1
```

Board-local edits to the USB-C receptacle have diverged from the library.
Confirm the divergence is intentional before fab.

## 12. Stale documentation

NEXT-STEPS.md §1 states "124 → 44 unconnected, **0 DRC errors**". The
unconnected count is still accurate at 44, but DRC now reports 9 violations.

---

## Confirmed correct — no action

These were checked and match their references. Recording them so they are not
re-examined.

- **nRF54L15 support topology matches Nordic's reference exactly.** DECA
  (pin 43) and DECRF (pin 33) are tied together with C2/C12/C5 — that is what
  Nordic's own schematic does, and was worth verifying because tying two
  regulator decoupling pins is usually wrong. FB1 bridging DECD→DECA, and
  DCC→L1→DECD with C1, also match.
- **All component values match Nordic's reference**, including the RF matching
  network down to the MPNs (LQP03HQ2N7B02, LQP03HQ3N5B02, GJM0335C1E1R5WB01,
  GJM0335C1E2R0WB01). Packages are upsized 0201→0402 (0603 for C3).
- **C6 and C9 isolated grounds are structurally correct.** Nordic requires C6's
  ground to reach only pin 32 (VSS_PA), and C9's ground to be isolated from all
  ground layers except the bottom. `/RF_PA_RETURN_LOCAL` (C6.2 + NT1 + U1.32) and
  `/RF_C9_RETURN_BOTTOM` (C9.2 + NT2, NT2 on B.Cu) implement both.
- **RF matching topology** — L2/L3/L4 in series from ANT with C6/C9 shunt and
  C11 shunt at the U.FL feed. Matches the reference.
- **D5 solar ORing polarity** — anode on `/SOLAR_5V`, cathode on `/VBUS_IN`.
  Solar can push into VBUS; USB cannot backfeed the panel.
- **BUCK2 topology** — SW2→L10→VOUT2=`/+3V3`, with C24 returned to
  `/GND_PVSS2` rather than plain GND. Correct.
- **Power gating chain** — `/+3V3` → U2.28 (LSIN1) → U2.29 (LSOUT1) →
  `/+3V3_FDC_SW` → U3.8. Matches HARDWARE.md §5.
- **All 57 no-connects are legitimate** — unused nRF54L15 GPIO (34), USB 3.x
  SuperSpeed and sideband pairs on J1 (14), unused nPM1300 BUCK1/LOADSW2/
  VBUSOUT/LED2/GPIO (11 across U2), FDC1004 CIN3/CIN4 (2), TPS7A1650
  DELAY/FB/NC/PG (4), Tag-Connect pins 7–8 (2).
- **ERC: 0 violations.**
- **Annotation: clean.**

---

## Recommended order for Phase 3

Findings 1, 2, 3 and 6 all sit in the power/PMIC and sense blocks and all
touch nets that currently have no copper. Doing power/PMIC first — as the
design already specifies — lets the L10 rotation, the VSET1 decision and the
BUCK2 loop tightening land before anything is routed around them.

Findings 4, 5 and 7 are the MCU block and are the largest placement change:
pulling C2/C12/C5 in from 8.2 mm, C3/C10 in from 9.4/5.1 mm, C1 in from
5.18 mm, and moving X2 closer with length-matched XC1/XC2.

Finding 2 is the sense block and is the only one that blocks the board's
primary function.
