alxgmpr/moisture-sensor/doc/enclosure-corner.png

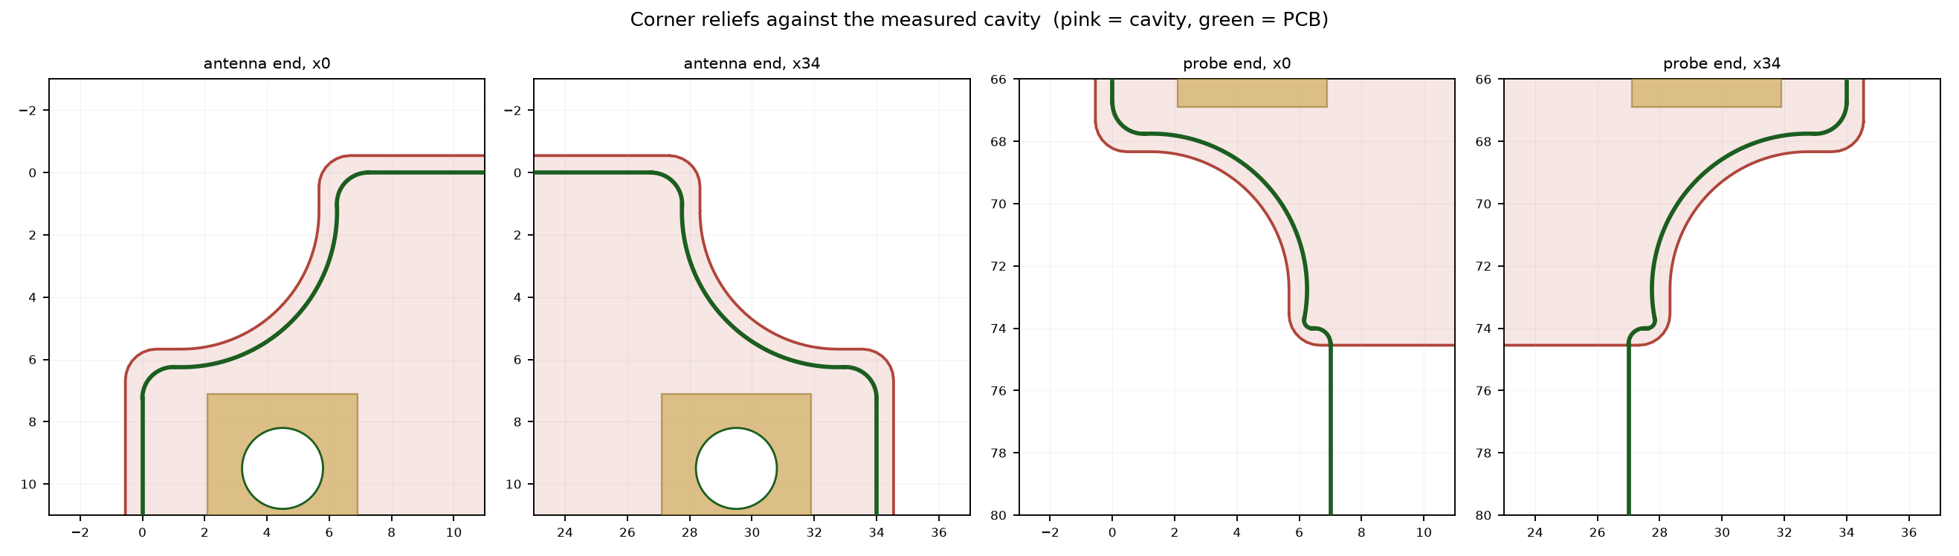
doc/enclosure-corner.png
