alxgmpr/moisture-sensor/doc/enclosure-fit.png

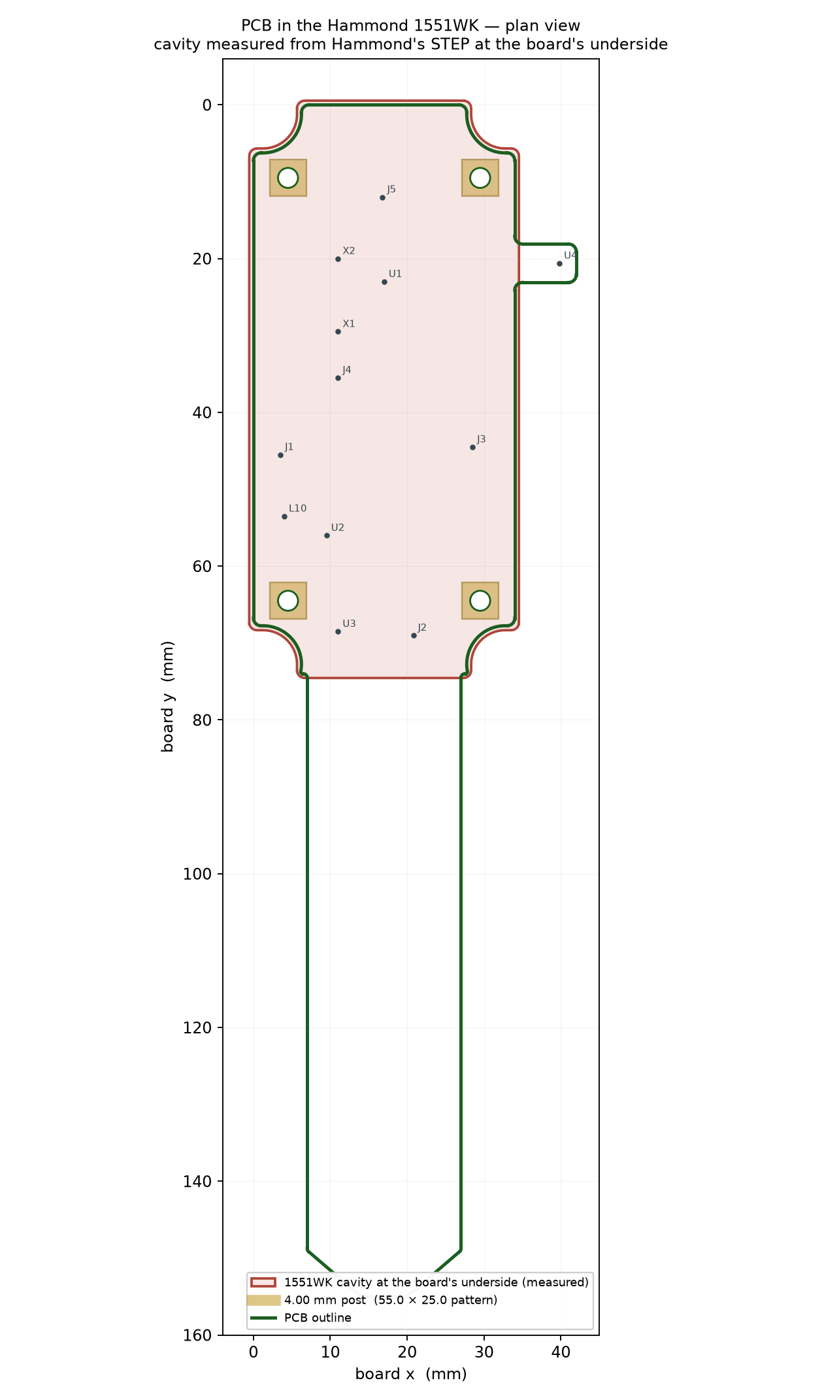
doc/enclosure-fit.png
