alxgmpr/moisture-sensor/doc/enclosure-section.png

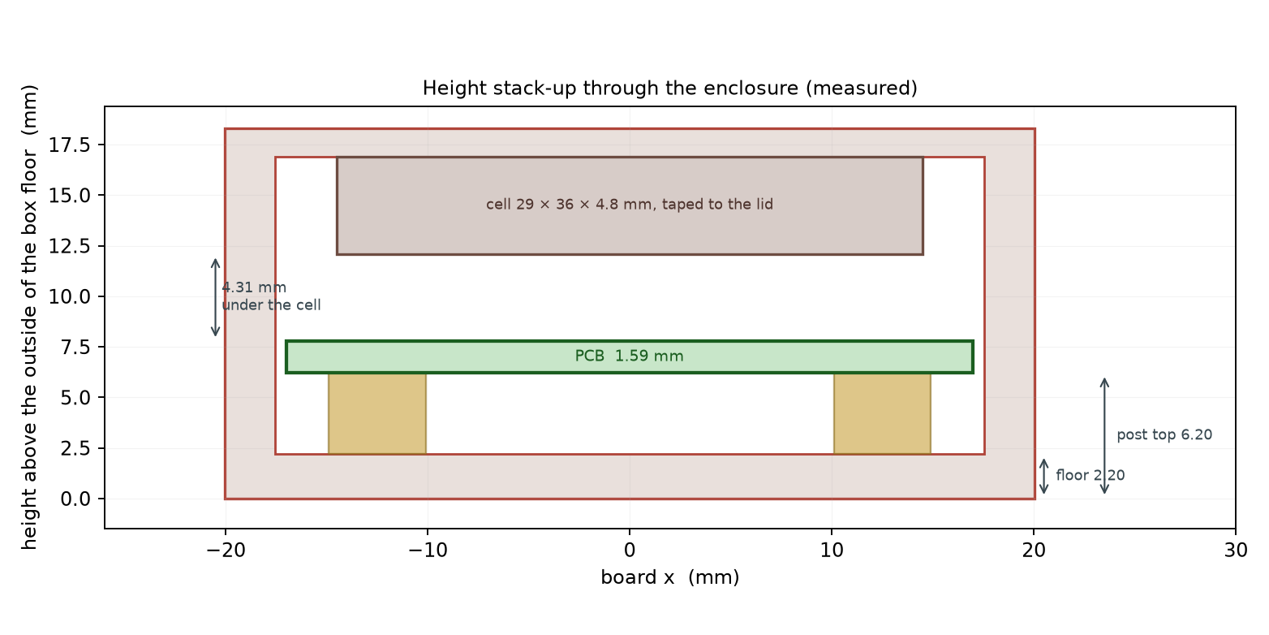
doc/enclosure-section.png
