alxgmpr/moisture-sensor/docs/audit-2026-09-06/electronics-3d.png

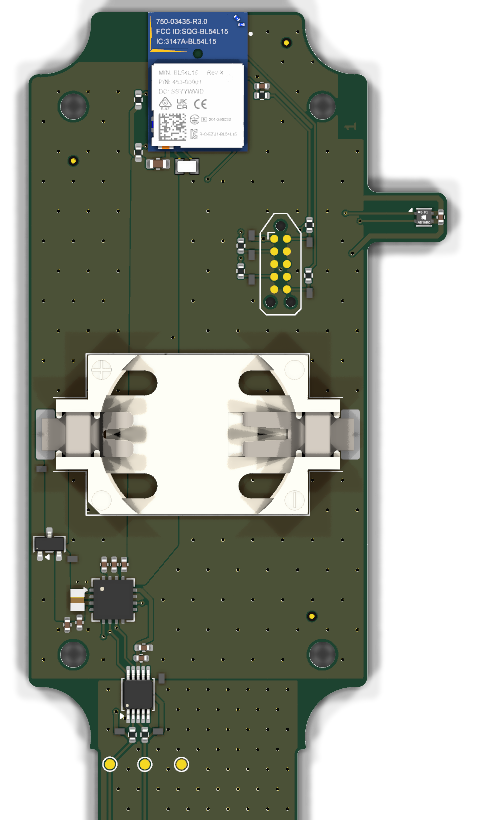
docs/audit-2026-09-06/electronics-3d.png
