alxgmpr/moisture-sensor/docs/audit-2026-09-06/layers.png

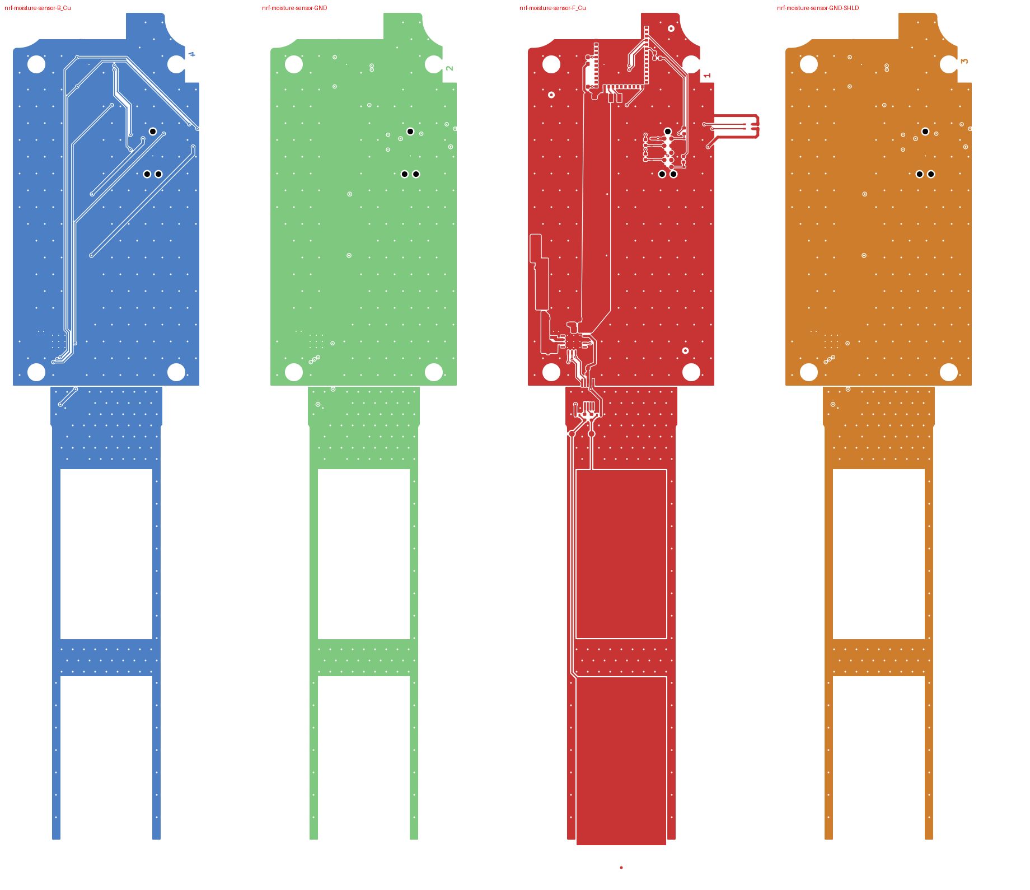
docs/audit-2026-09-06/layers.png
