alxgmpr/moisture-sensor/docs/audit-2026-09-06/layers/nrf-moisture-sensor-B_Cu.png

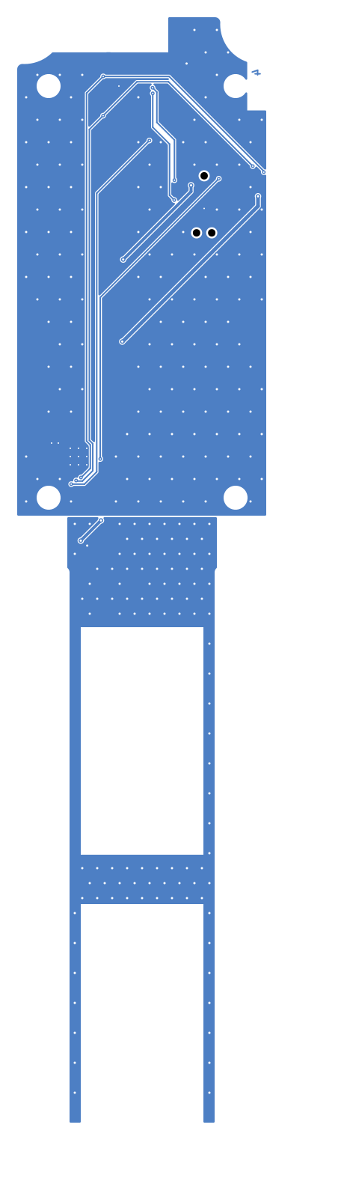
docs/audit-2026-09-06/layers/nrf-moisture-sensor-B_Cu.png
