alxgmpr/moisture-sensor/docs/audit-2026-09-06/layers/nrf-moisture-sensor-F_Cu.png

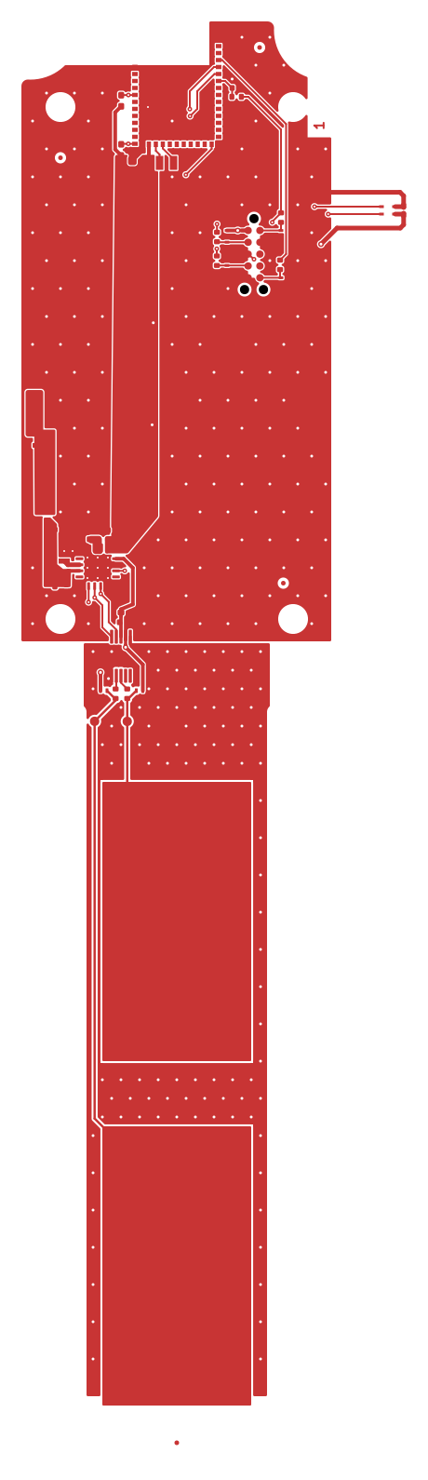
docs/audit-2026-09-06/layers/nrf-moisture-sensor-F_Cu.png
