alxgmpr/moisture-sensor/docs/audit-2026-09-06/layers/nrf-moisture-sensor-GND-SHLD.png

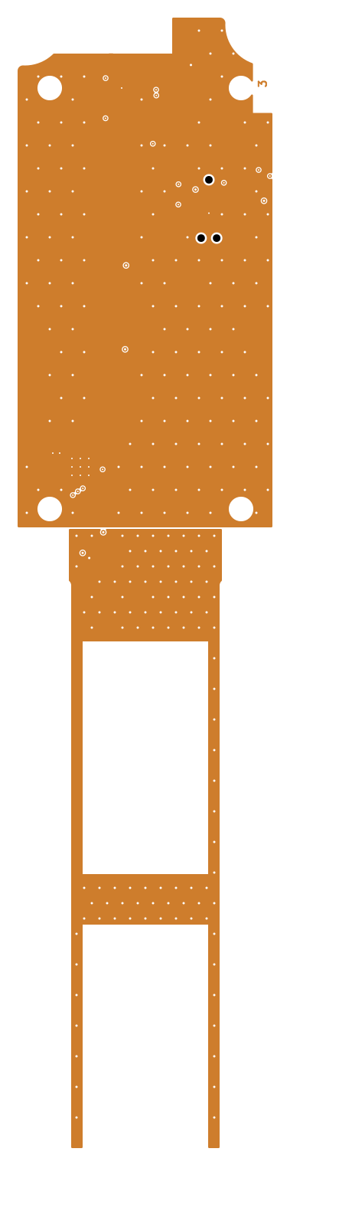
docs/audit-2026-09-06/layers/nrf-moisture-sensor-GND-SHLD.png
