alxgmpr/moisture-sensor/docs/audit-2026-09-06/schematic.png

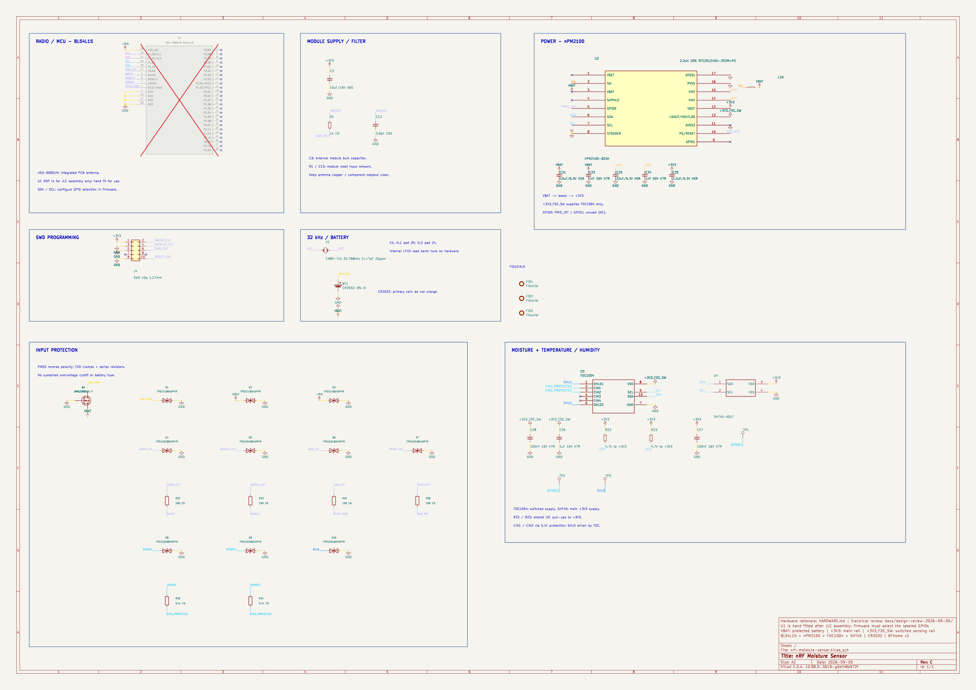
docs/audit-2026-09-06/schematic.png
