alxgmpr/moisture-sensor/docs/bl54l15/B_Cu.png

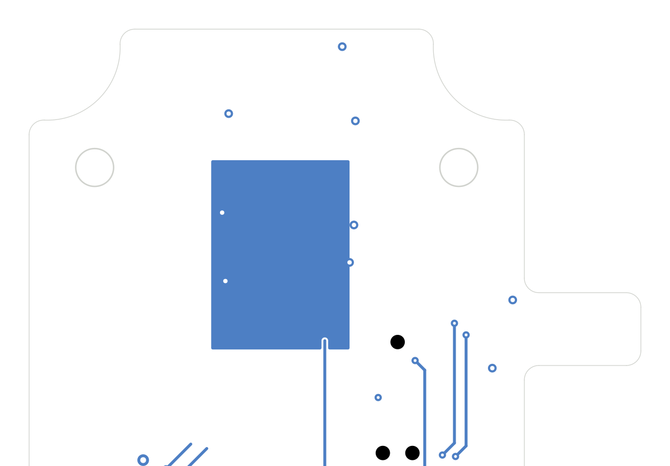
docs/bl54l15/B_Cu.png
