alxgmpr/moisture-sensor/docs/bl54l15/F_Cu.png

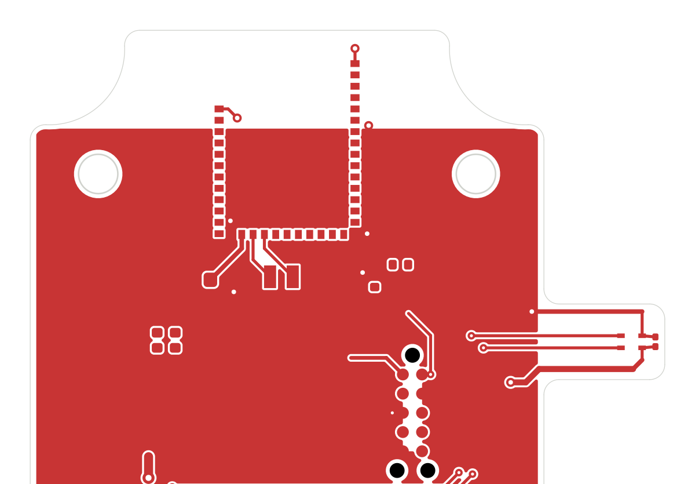
docs/bl54l15/F_Cu.png
