alxgmpr/moisture-sensor/docs/bl54l15/F_Mask.png

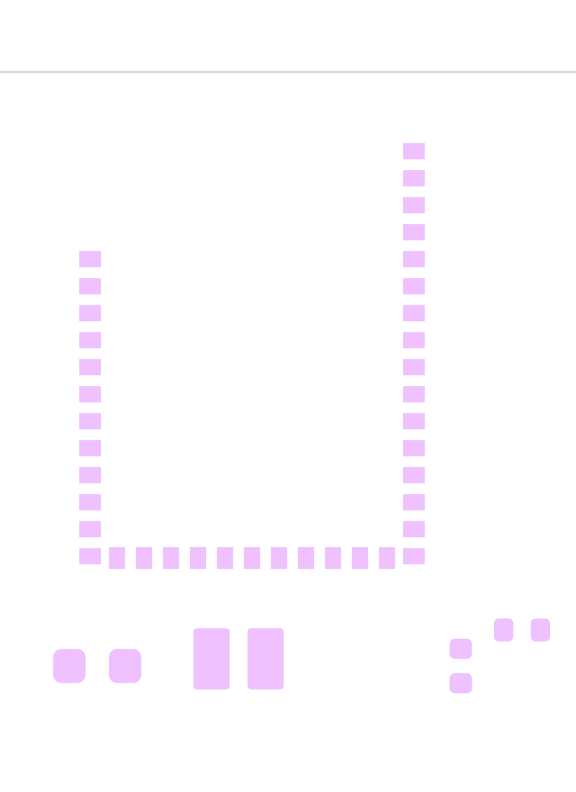
docs/bl54l15/F_Mask.png
