alxgmpr/moisture-sensor/docs/bl54l15/GND.png

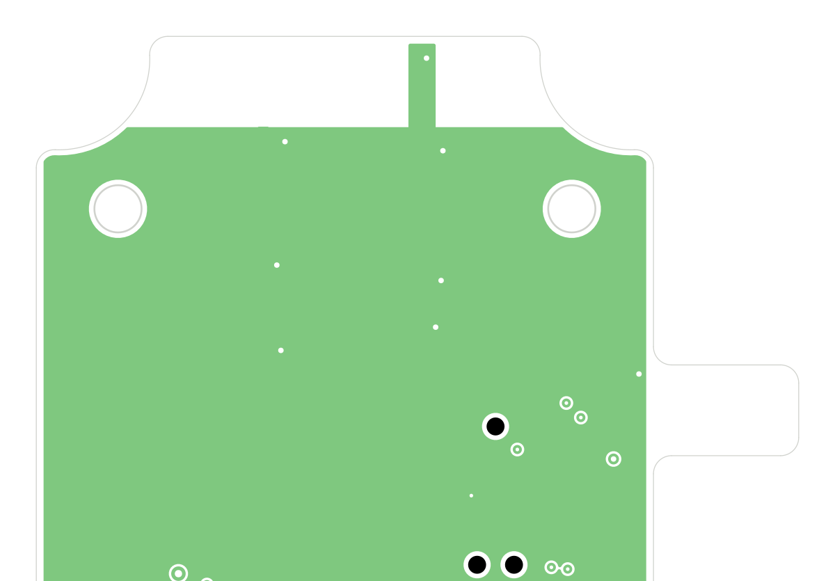
docs/bl54l15/GND.png
