alxgmpr/moisture-sensor/docs/bl54l15/PWR-SHLD.png

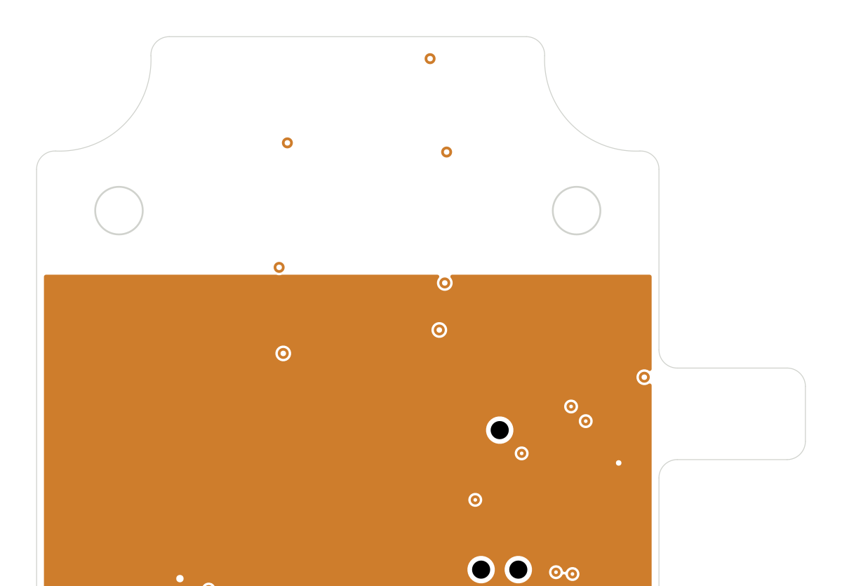
docs/bl54l15/PWR-SHLD.png
