alxgmpr/moisture-sensor/docs/bl54l15/schematic-module.png

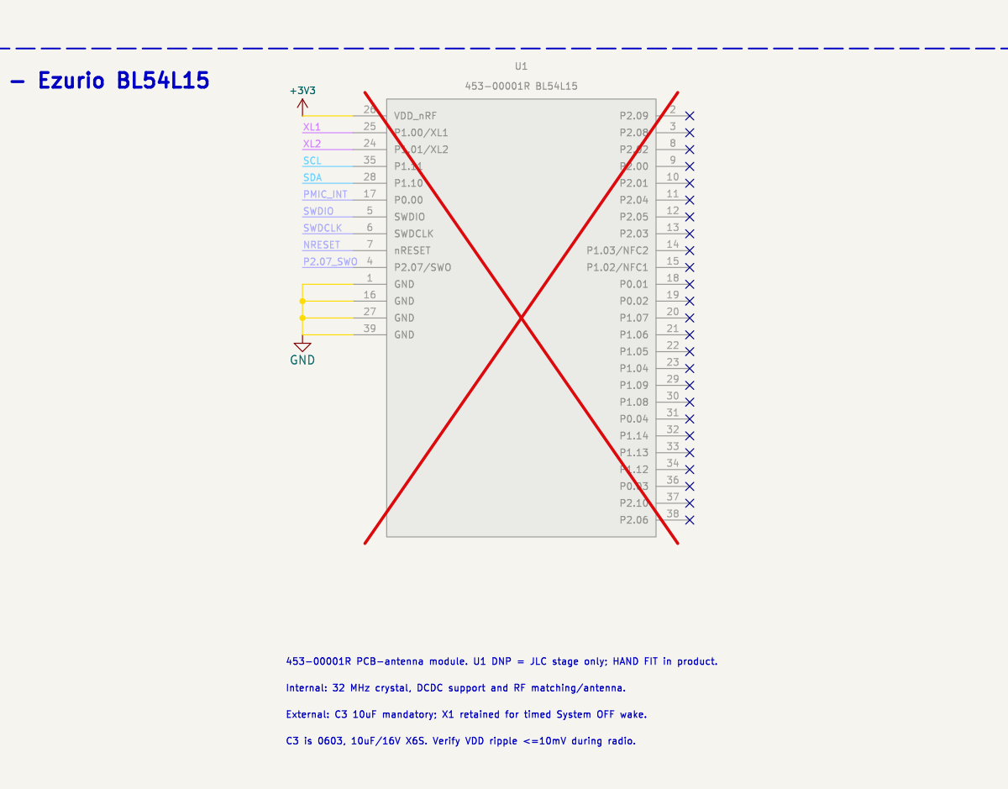
docs/bl54l15/schematic-module.png
