alxgmpr/moisture-sensor/docs/cost-reduction-2026-09-09/schematic.png

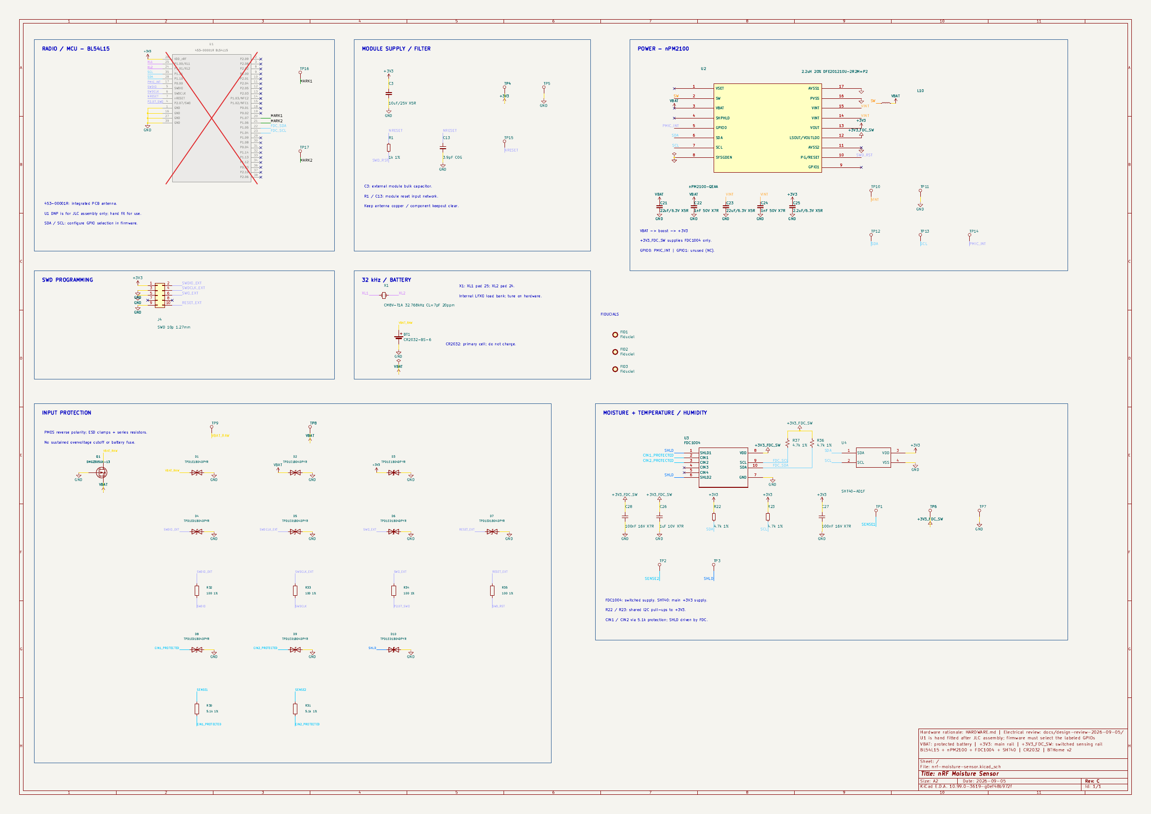
docs/cost-reduction-2026-09-09/schematic.png
