alxgmpr/moisture-sensor/docs/design-review-2026-09-05/board-3d.png

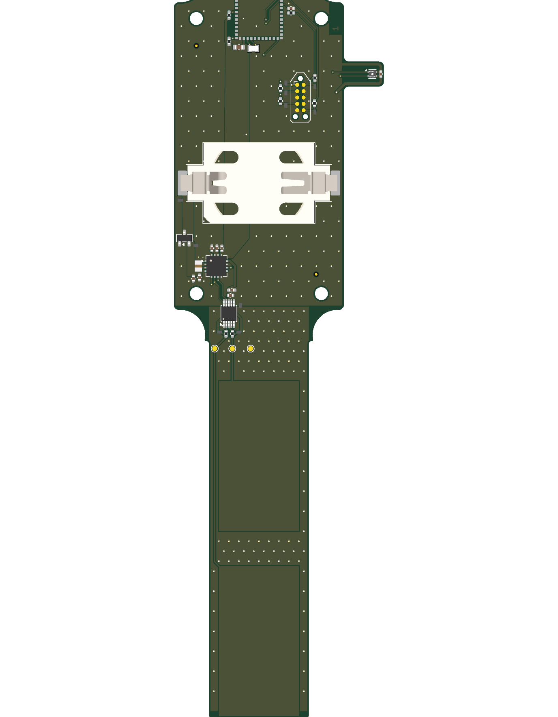
docs/design-review-2026-09-05/board-3d.png
