alxgmpr/moisture-sensor/docs/design-review-2026-09-05/layers-overview.png

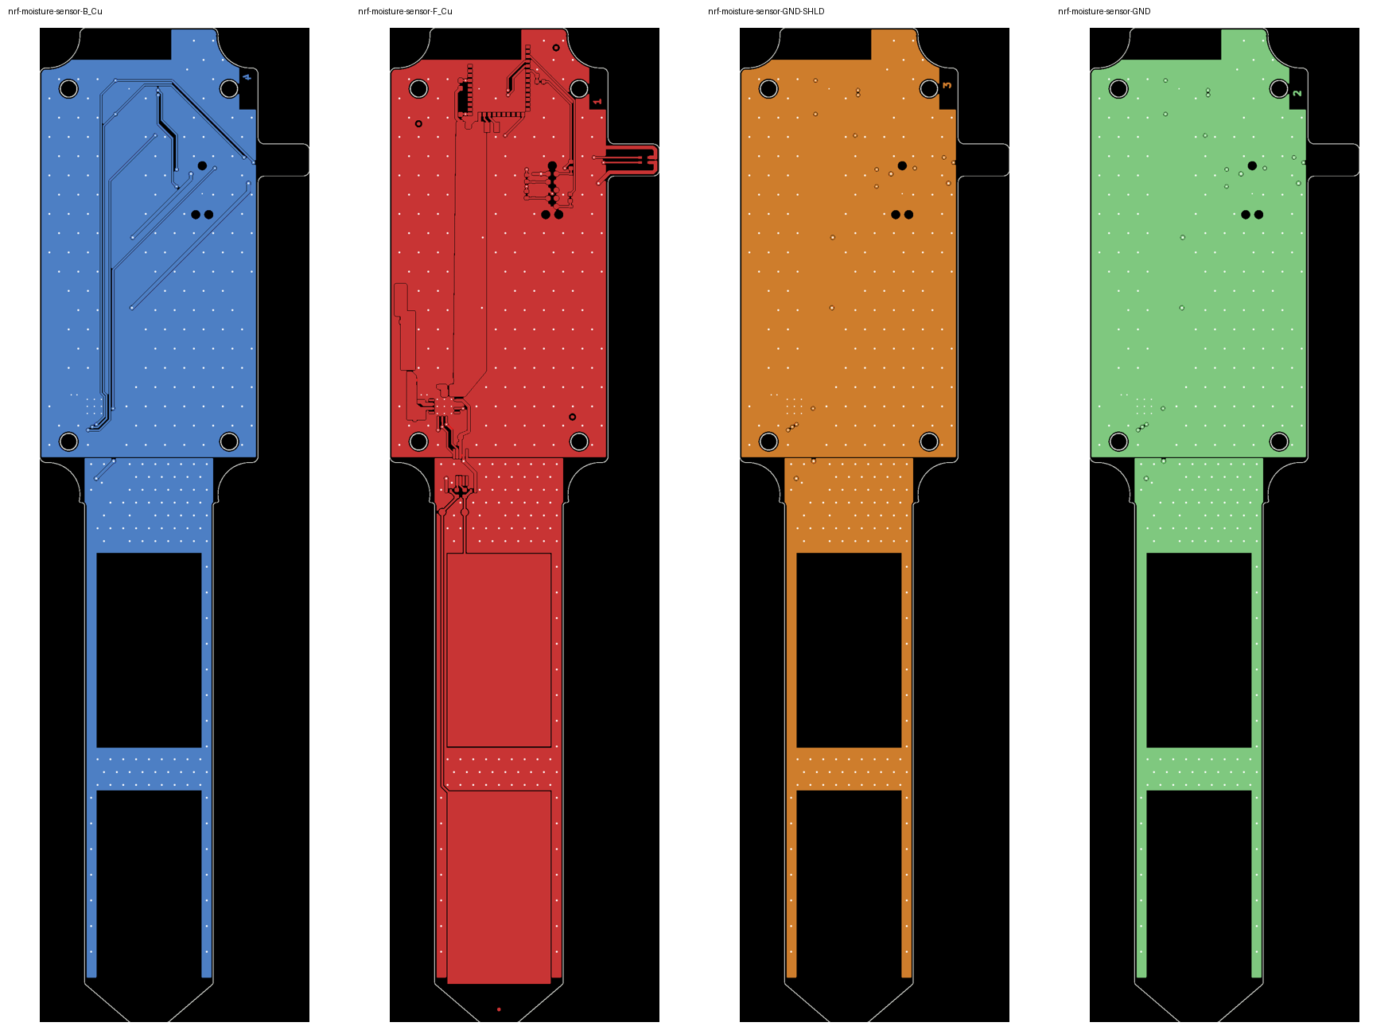
docs/design-review-2026-09-05/layers-overview.png
