alxgmpr/moisture-sensor/docs/fdc-bus-feasibility-2026-09-09/B_Cu-module.png

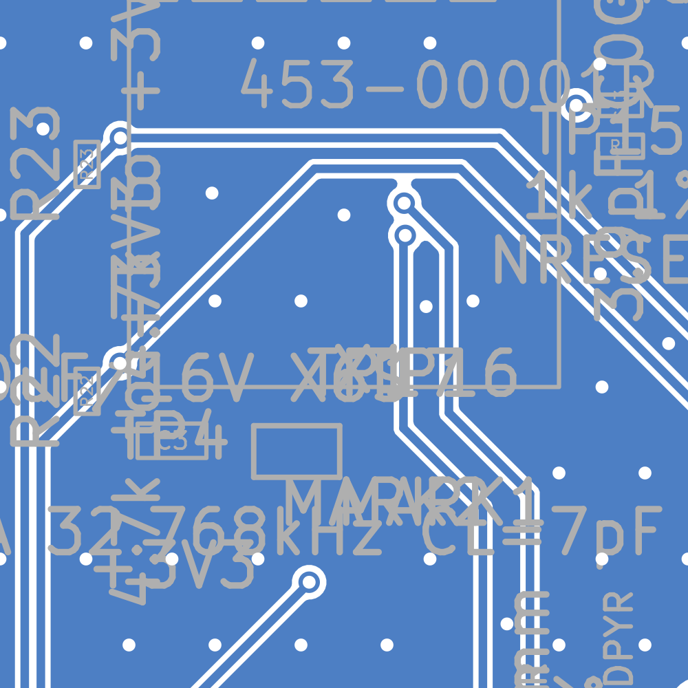
docs/fdc-bus-feasibility-2026-09-09/B_Cu-module.png
