alxgmpr/moisture-sensor/docs/fdc-bus-feasibility-2026-09-09/escape-B_Cu.png

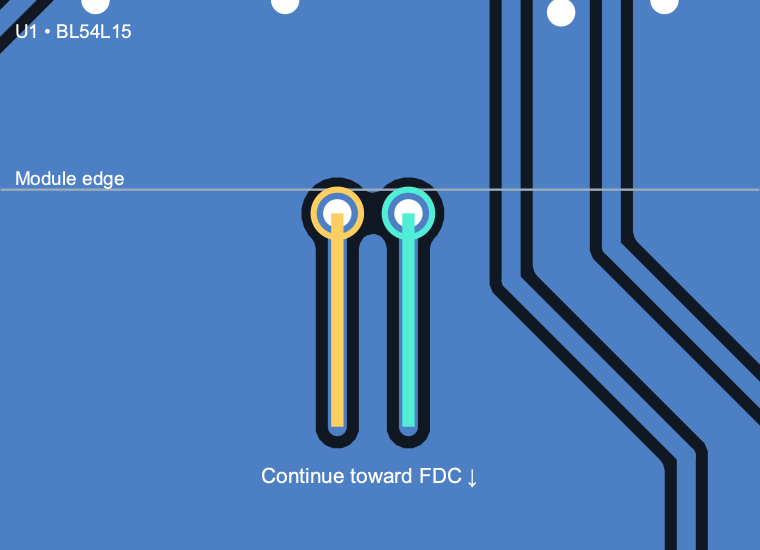
docs/fdc-bus-feasibility-2026-09-09/escape-B_Cu.png
