alxgmpr/moisture-sensor/docs/fdc-bus-feasibility-2026-09-09/F_Cu-path.png

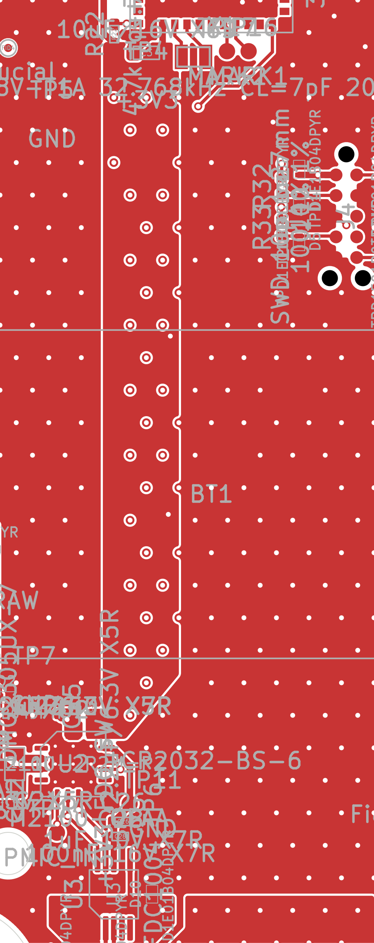
docs/fdc-bus-feasibility-2026-09-09/F_Cu-path.png
