alxgmpr/moisture-sensor/docs/fdc-bus-update-2026-09-09/before/ble.png

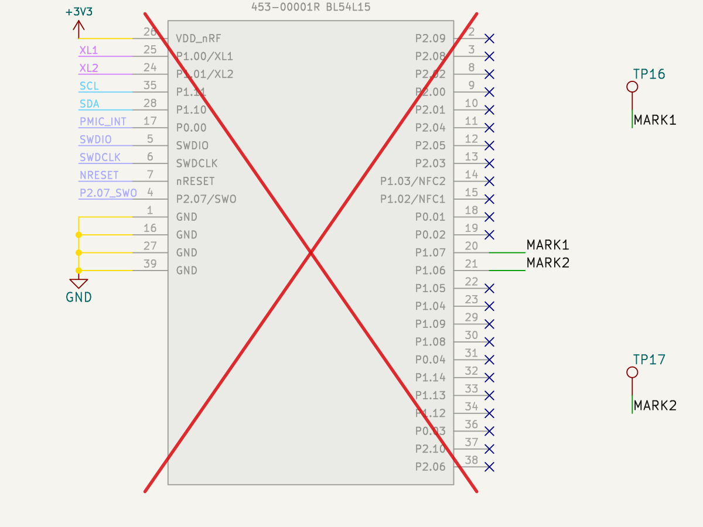
docs/fdc-bus-update-2026-09-09/before/ble.png
