alxgmpr/moisture-sensor/docs/fdc-bus-update-2026-09-09/ble.png

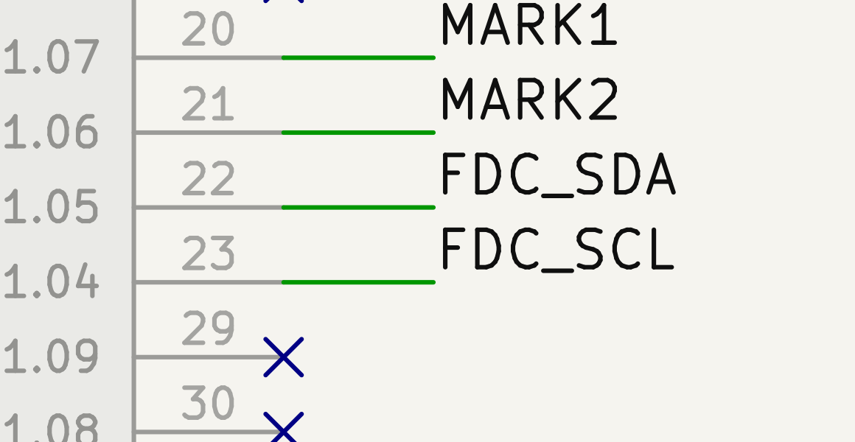
docs/fdc-bus-update-2026-09-09/ble.png
