alxgmpr/moisture-sensor/docs/footprint-review-2026-09-09/front-copper.png

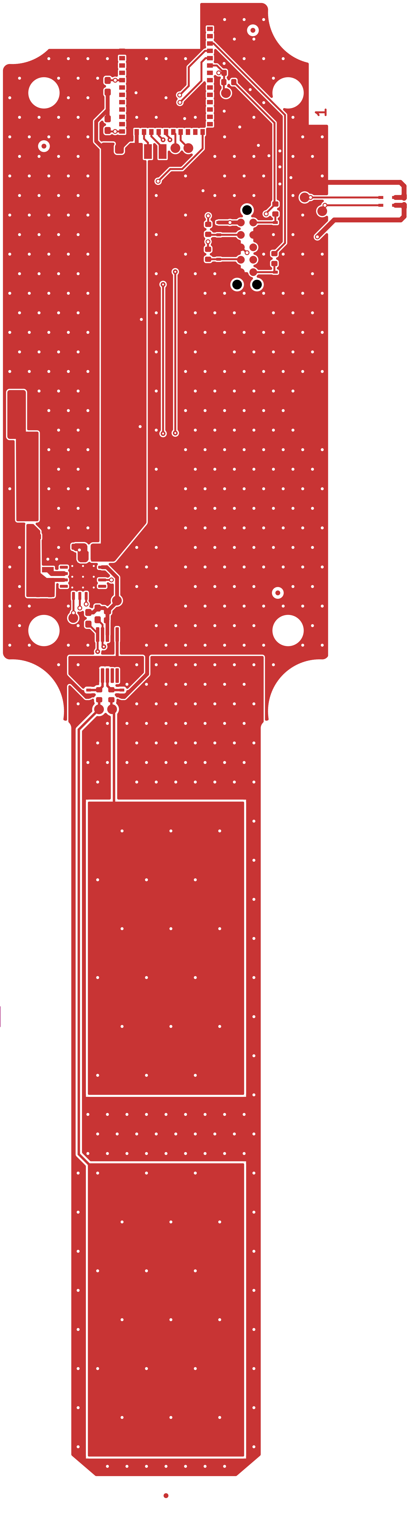
docs/footprint-review-2026-09-09/front-copper.png
