alxgmpr/moisture-sensor/docs/footprint-review-2026-09-09/power-3d.png

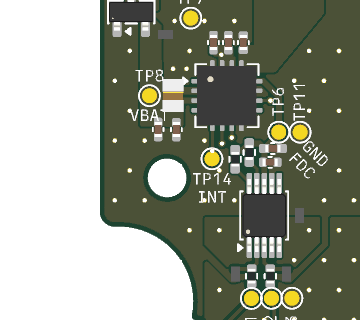
docs/footprint-review-2026-09-09/power-3d.png
