alxgmpr/moisture-sensor/docs/footprint-review-2026-09-09/top.png

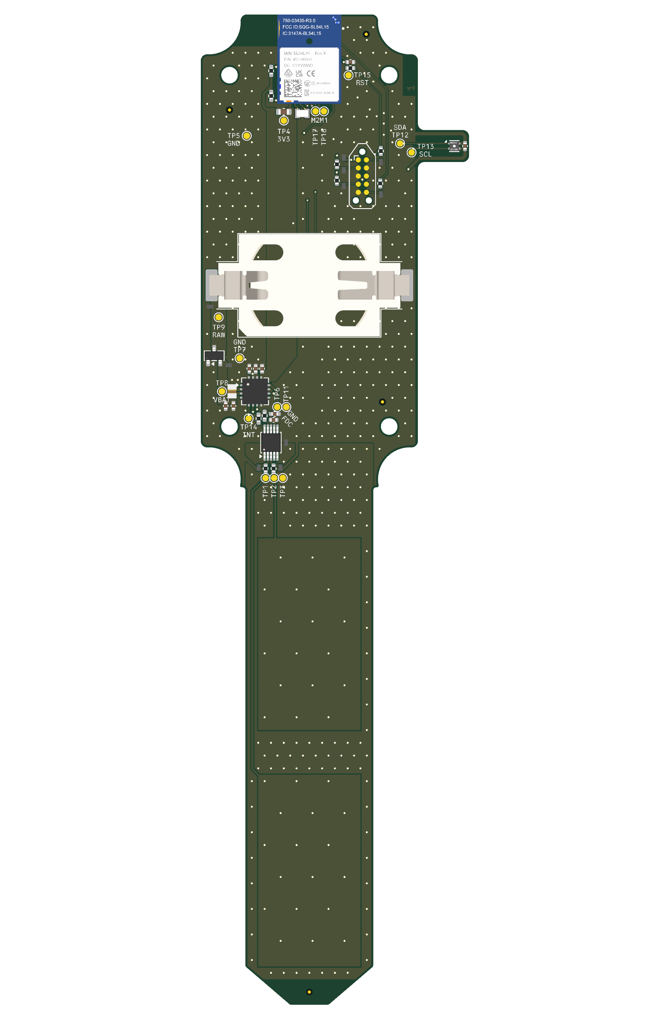
docs/footprint-review-2026-09-09/top.png
