alxgmpr/moisture-sensor/docs/footprint-standardization-2026-09-09/power-copper.png

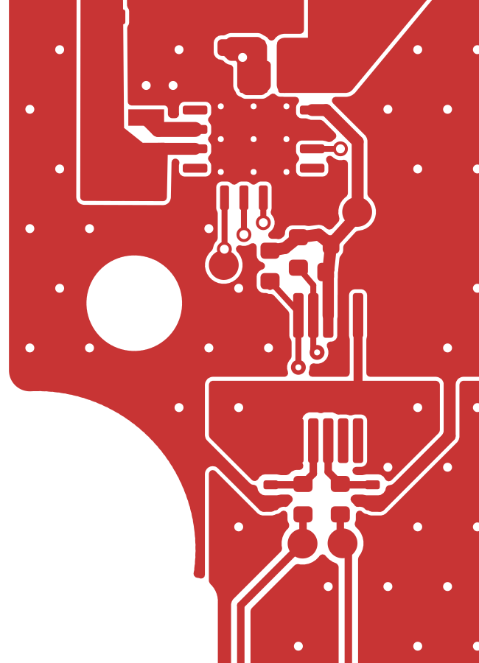
docs/footprint-standardization-2026-09-09/power-copper.png
