alxgmpr/moisture-sensor/docs/in2-ground/layers.png

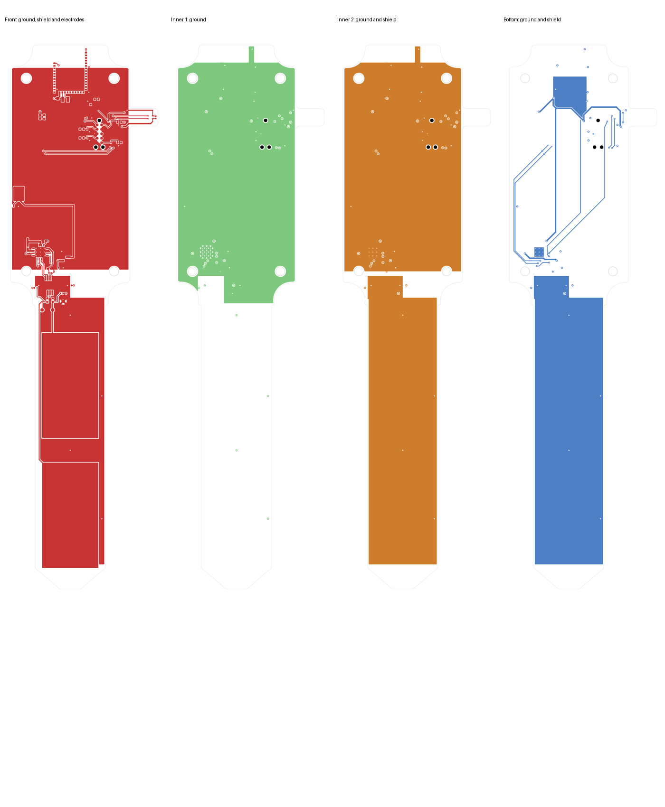
docs/in2-ground/layers.png
