alxgmpr/moisture-sensor/docs/jlc-fiducial-removal-2026-09-09/front-mask.png

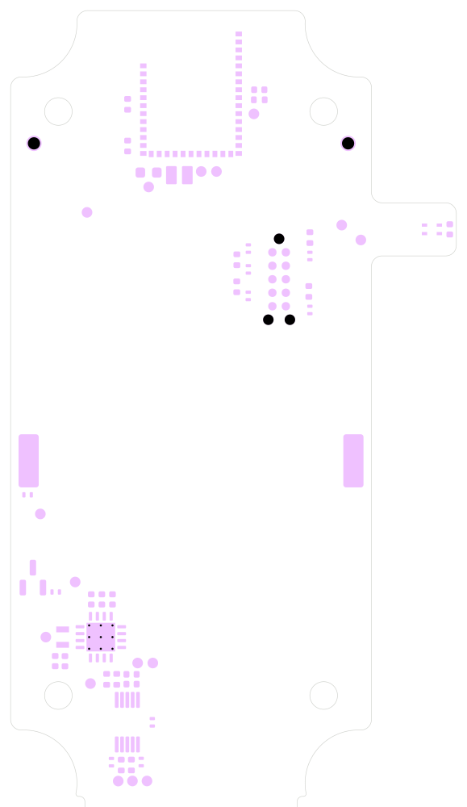
docs/jlc-fiducial-removal-2026-09-09/front-mask.png
