alxgmpr/moisture-sensor/docs/jlc-fiducials-2026-09-09/mask-gerber.png

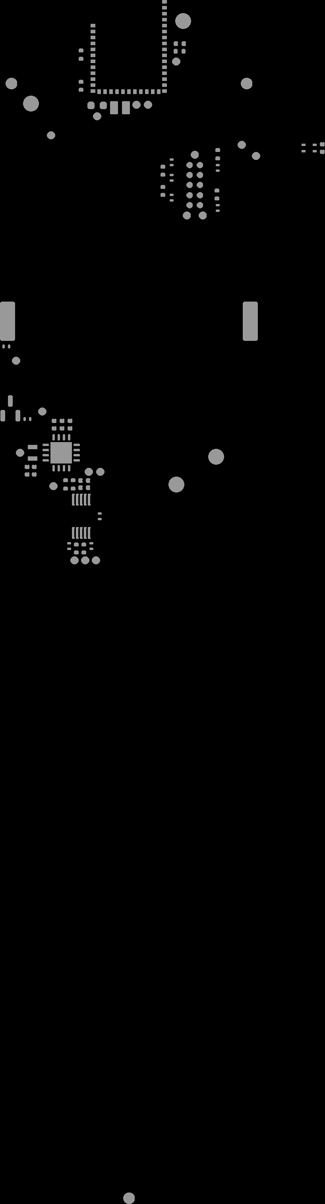
docs/jlc-fiducials-2026-09-09/mask-gerber.png
