alxgmpr/moisture-sensor/docs/probe-review-2026-09-09/layers.png

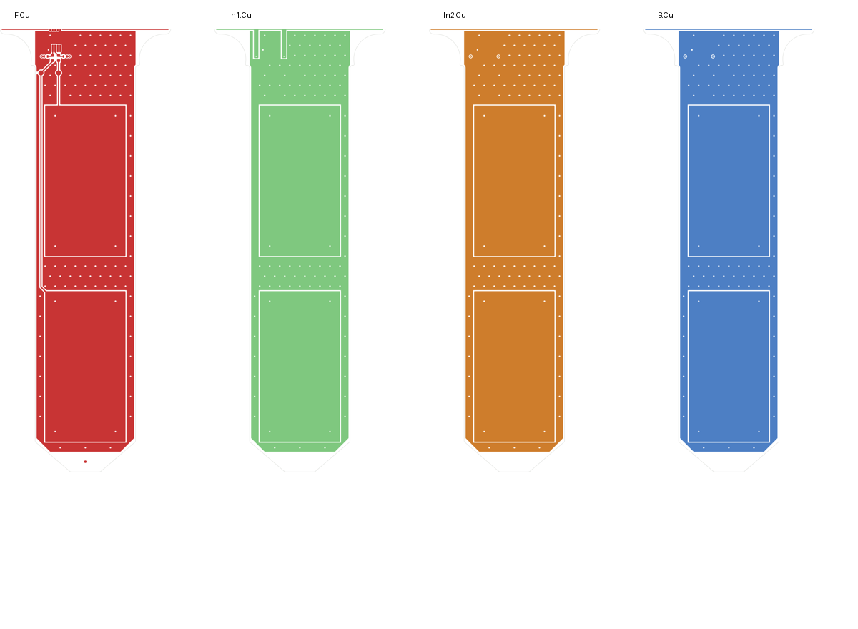
docs/probe-review-2026-09-09/layers.png
