alxgmpr/moisture-sensor/docs/probe-review-2026-09-09/protection.png

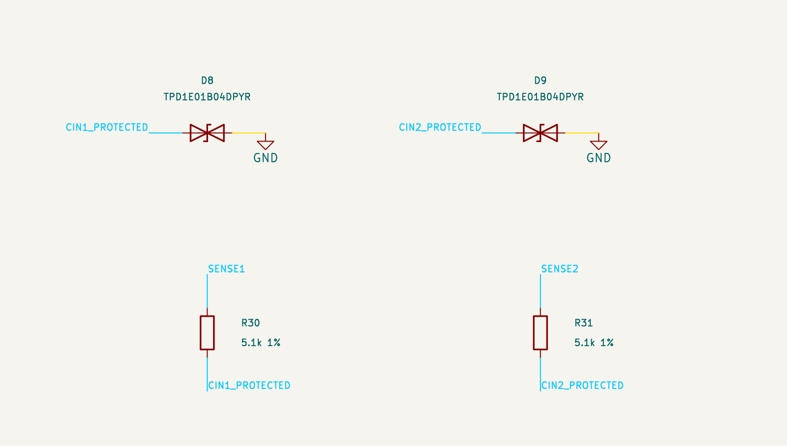
docs/probe-review-2026-09-09/protection.png
