alxgmpr/moisture-sensor/docs/protection/diode-front/courtyard.png

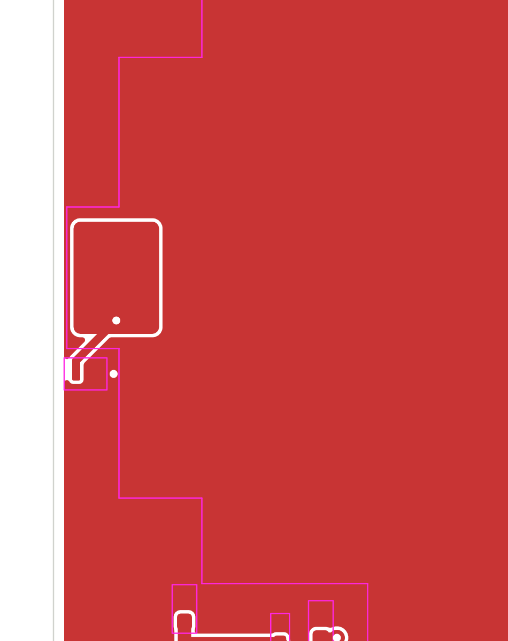
docs/protection/diode-front/courtyard.png
