alxgmpr/moisture-sensor/docs/protection/diode-front/model-preview.png

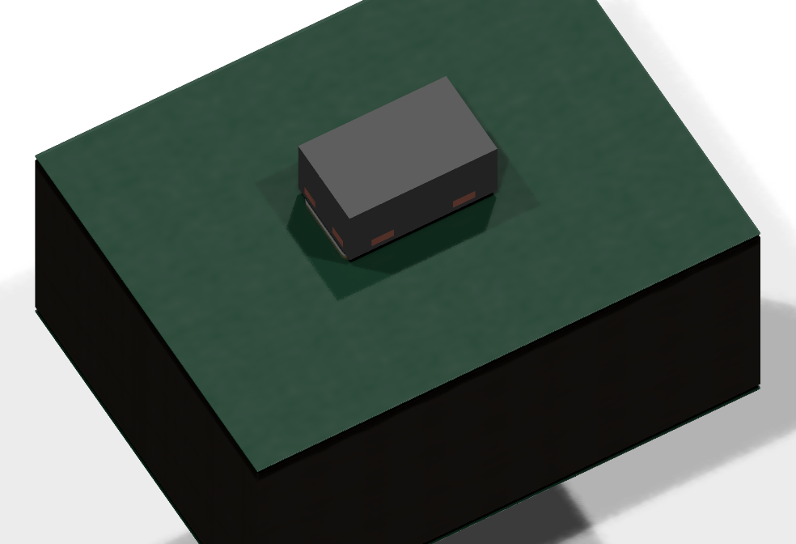
docs/protection/diode-front/model-preview.png
