alxgmpr/moisture-sensor/docs/protection/layout-power.png

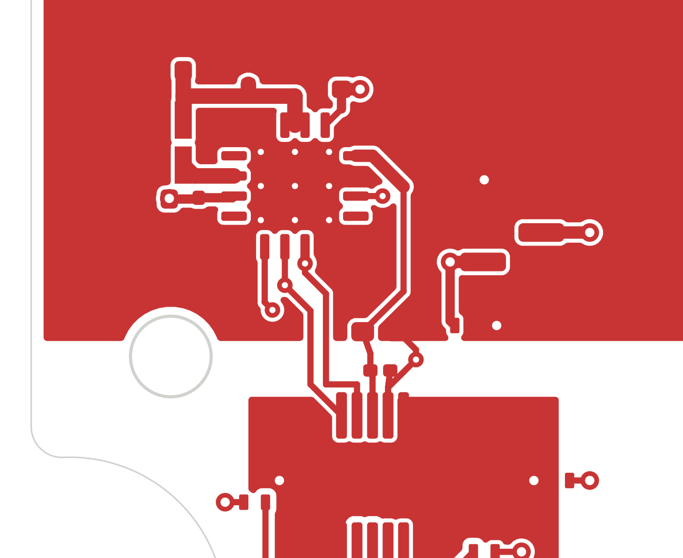
docs/protection/layout-power.png
