alxgmpr/moisture-sensor/docs/protection/layout-probe.png

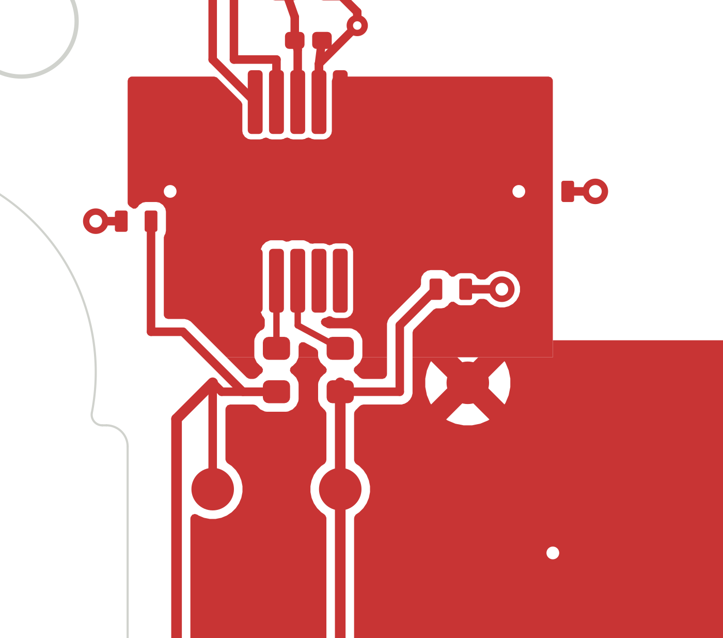
docs/protection/layout-probe.png
