alxgmpr/moisture-sensor/docs/protection/schematic.png

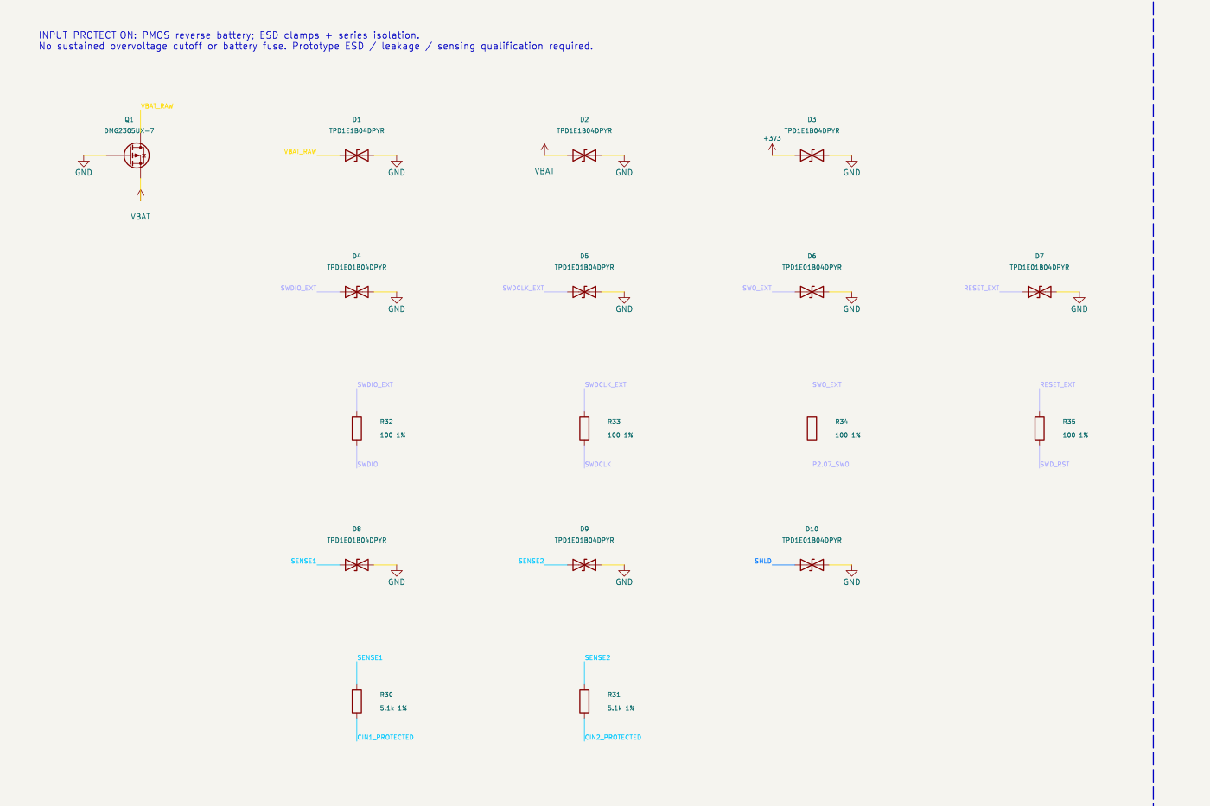
docs/protection/schematic.png
