alxgmpr/moisture-sensor/docs/reliability-2026-09-07/layers/nrf-moisture-sensor-B_Cu-detail.png

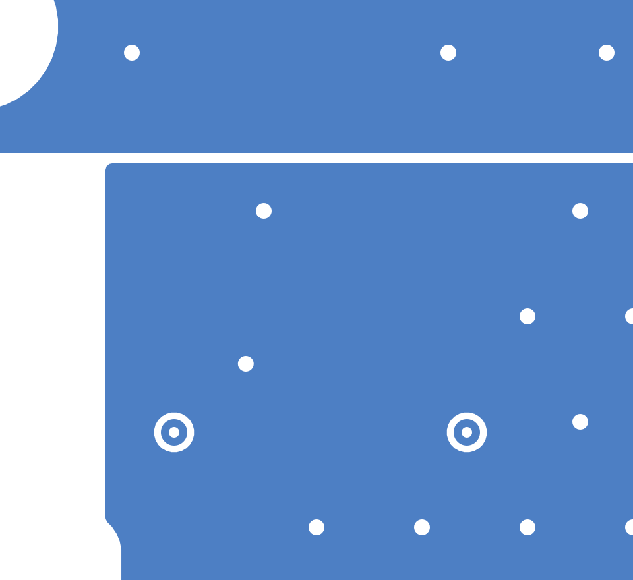
docs/reliability-2026-09-07/layers/nrf-moisture-sensor-B_Cu-detail.png
