alxgmpr/moisture-sensor/docs/reliability-2026-09-07/simulation.png

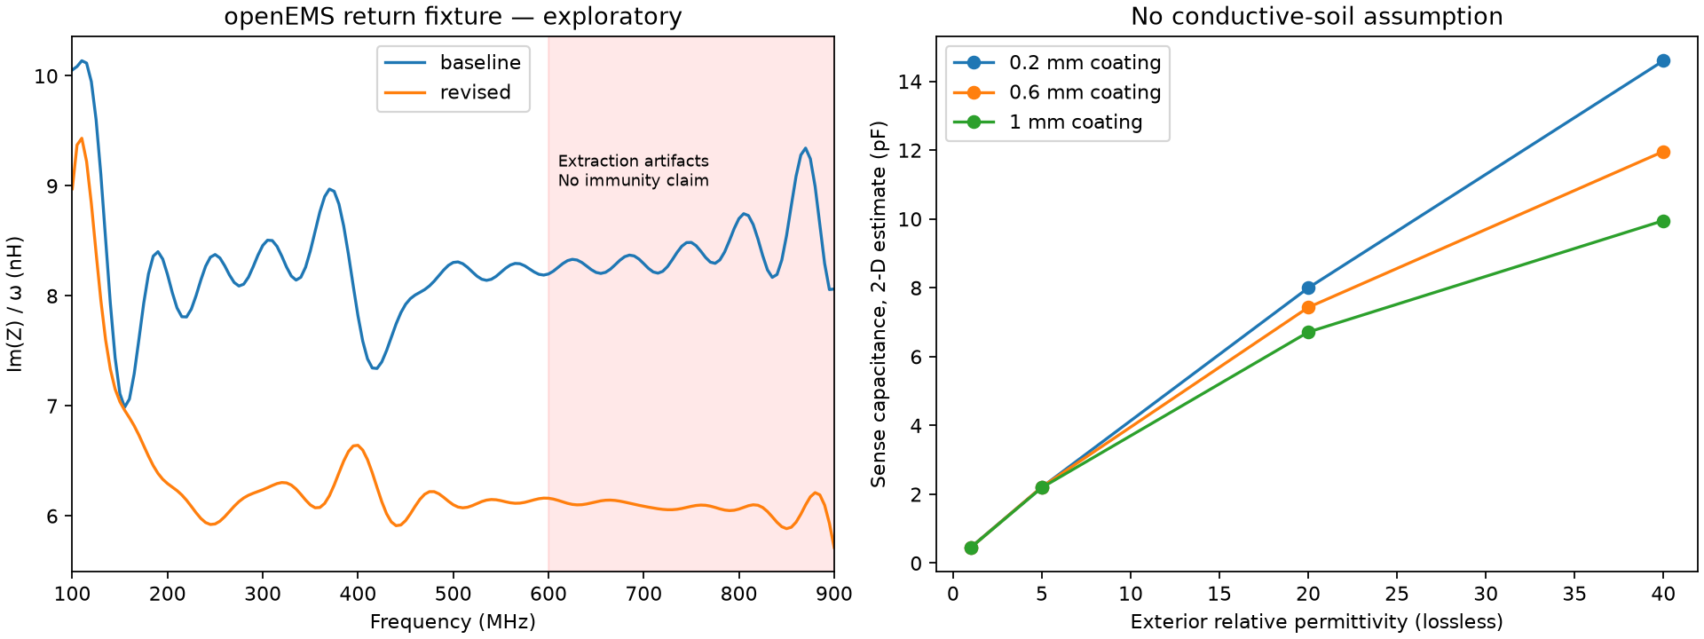
docs/reliability-2026-09-07/simulation.png
