alxgmpr/moisture-sensor/docs/schematic-review-2026-09-05/after/radio.png

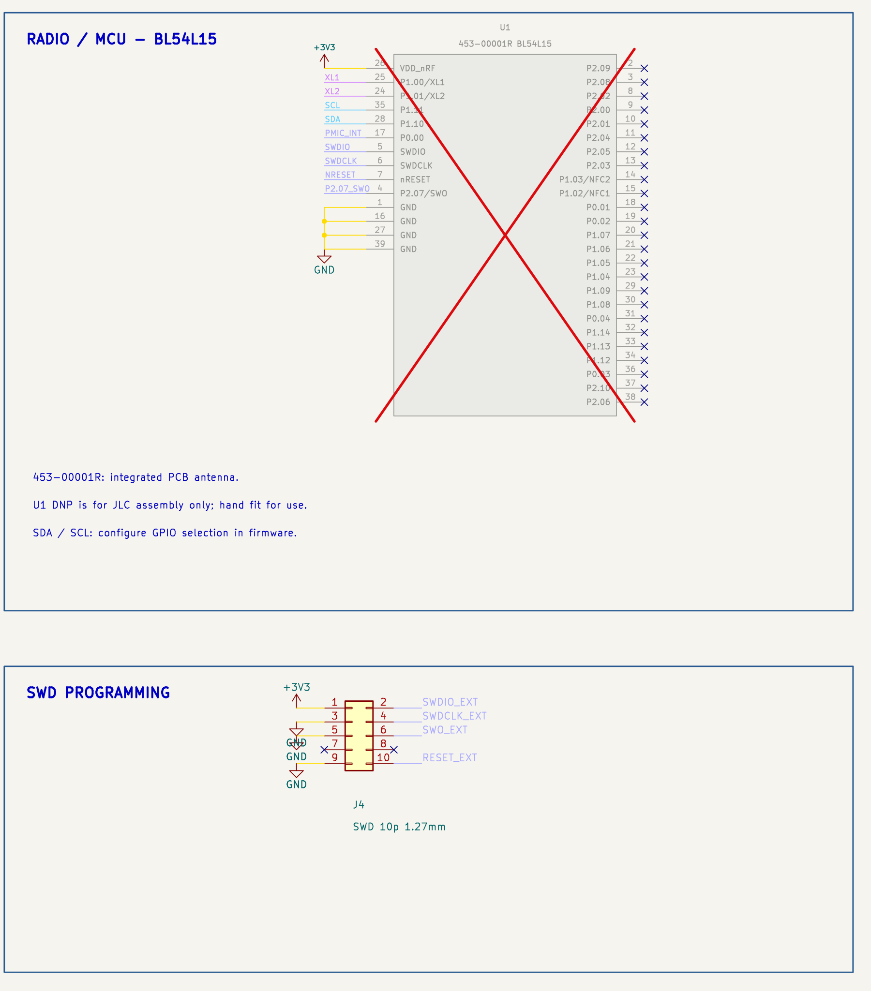
docs/schematic-review-2026-09-05/after/radio.png
