alxgmpr/moisture-sensor/docs/schematic-review-2026-09-05/after/support.png

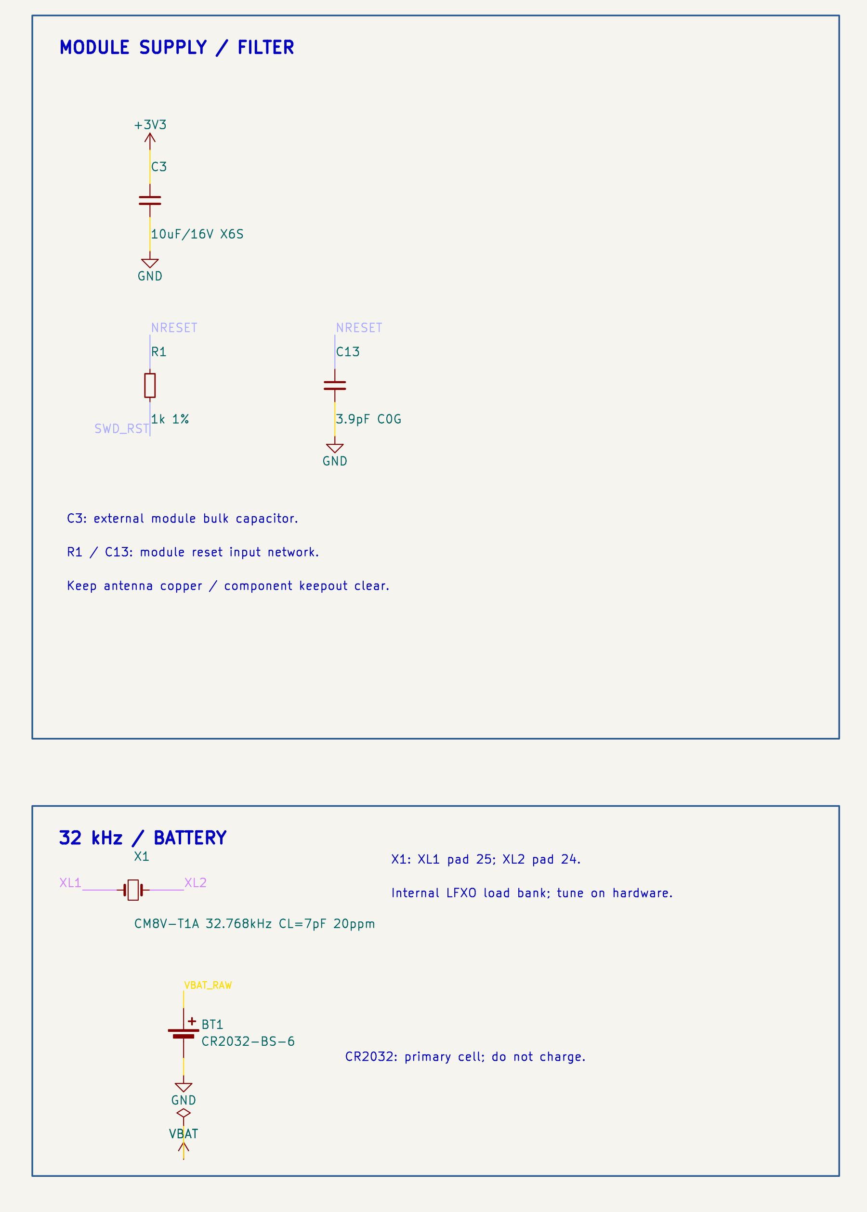
docs/schematic-review-2026-09-05/after/support.png
