alxgmpr/moisture-sensor/docs/cost-reduction-2026-09-09/sensor-detail.png

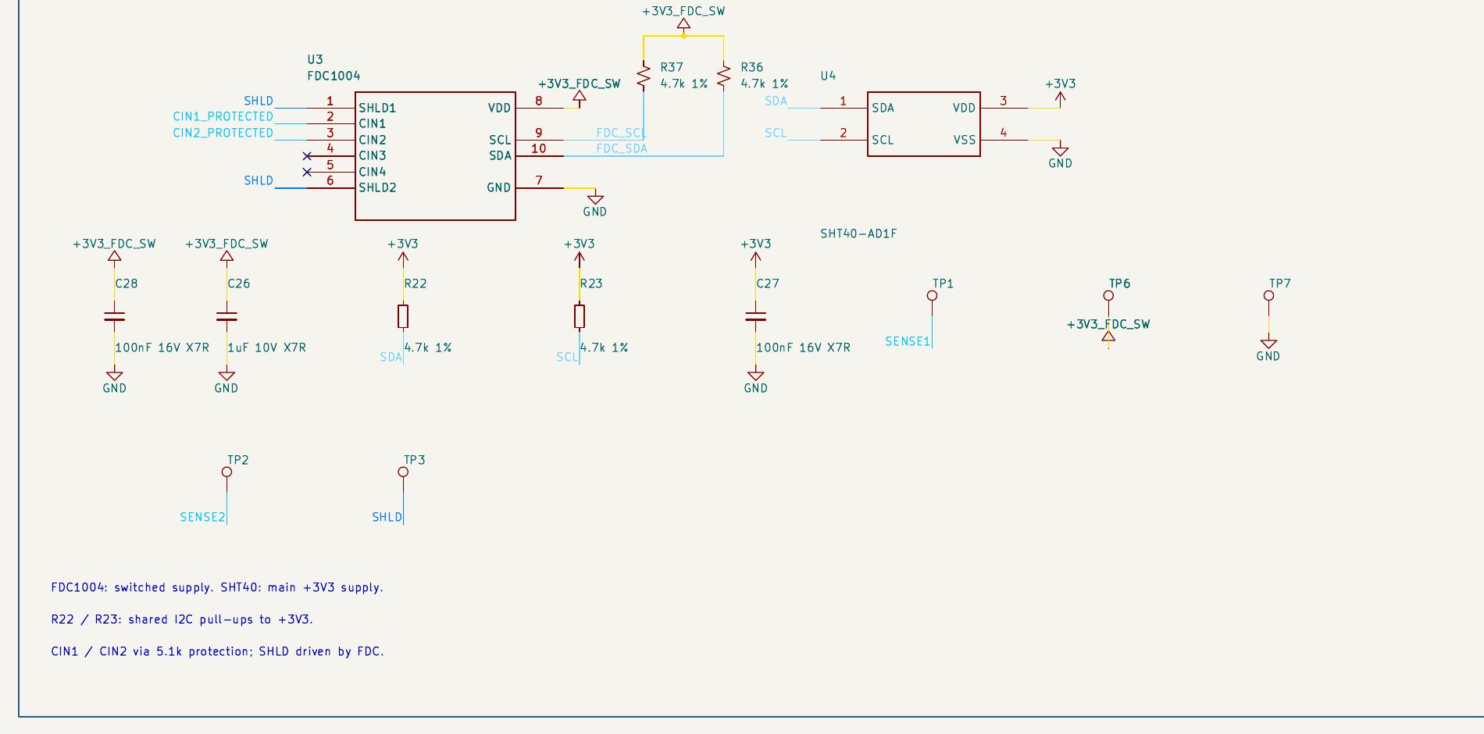
docs/cost-reduction-2026-09-09/sensor-detail.png
