alxgmpr/moisture-sensor/docs/testpoints-2026-09-07/assembled-head.png

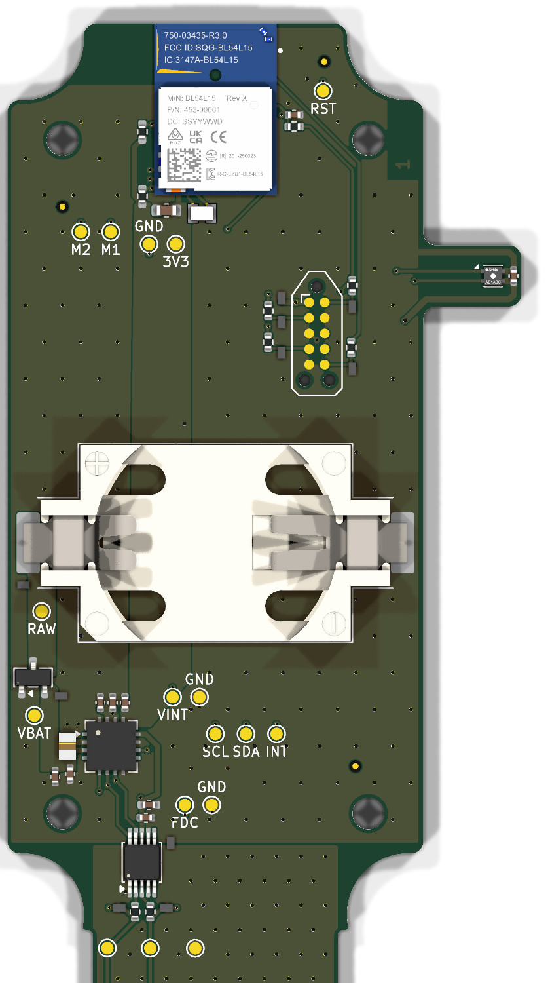
docs/testpoints-2026-09-07/assembled-head.png
