alxgmpr/moisture-sensor/docs/wiring-review-2026-09-09/assembly.png

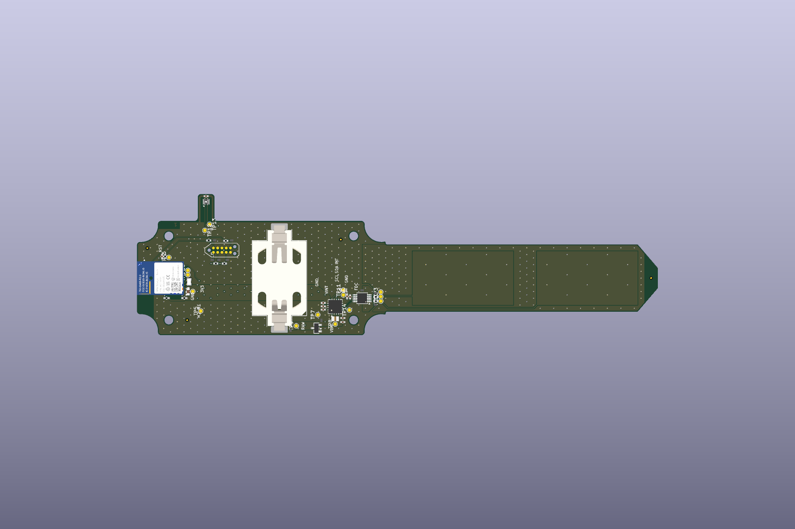
docs/wiring-review-2026-09-09/assembly.png
