alxgmpr/moisture-sensor/docs/wiring-review-2026-09-09/copper.png

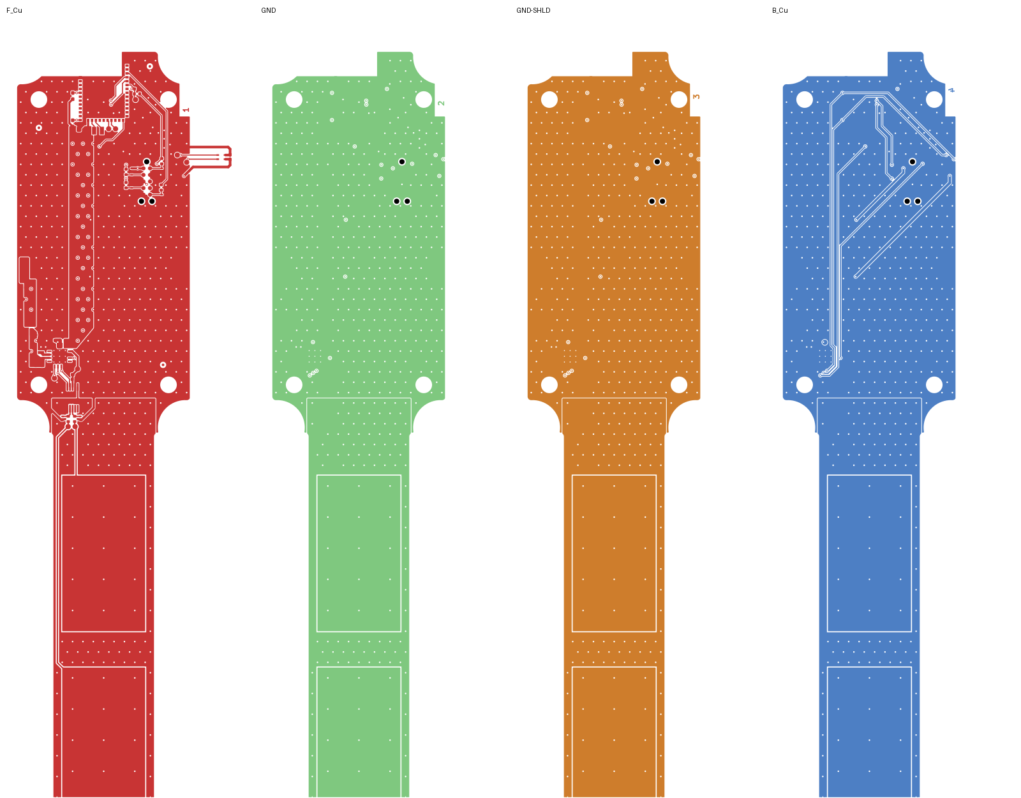
docs/wiring-review-2026-09-09/copper.png
