alxgmpr/moisture-sensor/docs/wiring-review-2026-09-09/esd-returns.png

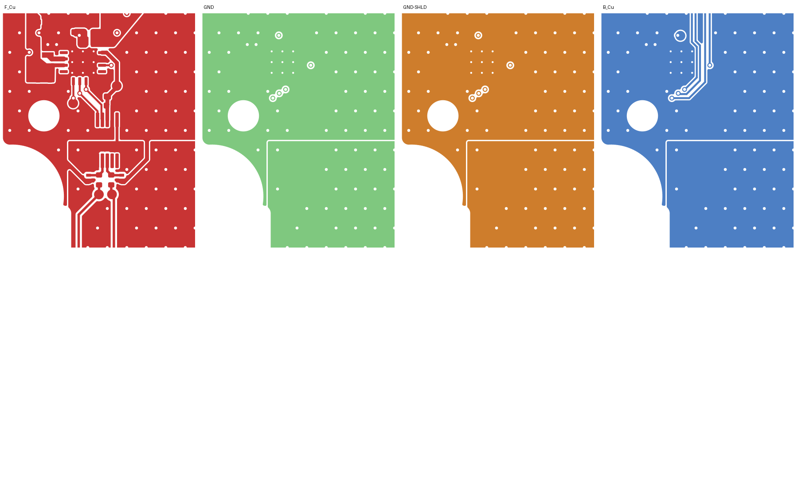
docs/wiring-review-2026-09-09/esd-returns.png
