alxgmpr/moisture-sensor/docs/wiring-review-2026-09-09/F_Cu-detail.png

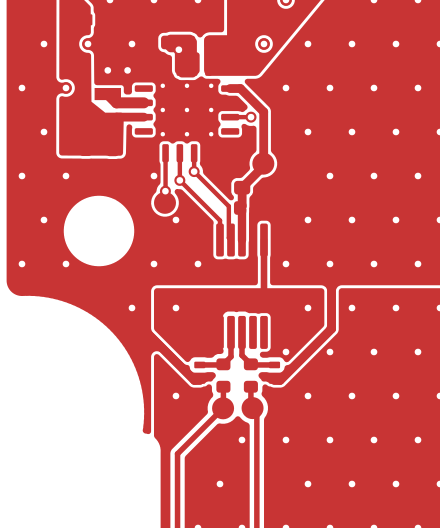
docs/wiring-review-2026-09-09/F_Cu-detail.png
