alxgmpr/moisture-sensor/docs/wiring-review-2026-09-09/GND-board.png

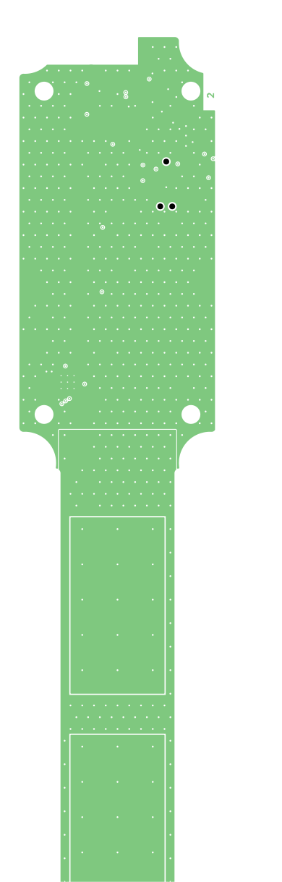
docs/wiring-review-2026-09-09/GND-board.png
