alxgmpr/moisture-sensor/docs/wiring-review-2026-09-09/GND-SHLD-detail.png

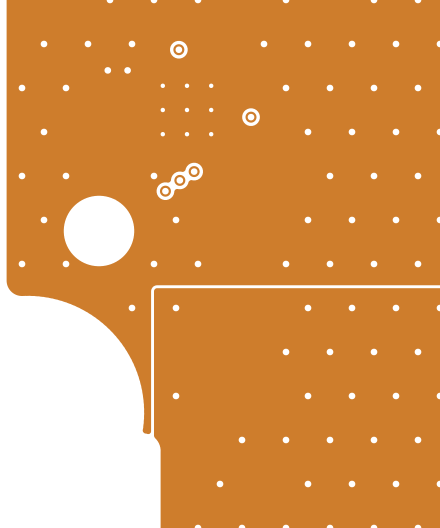
docs/wiring-review-2026-09-09/GND-SHLD-detail.png
