alxgmpr/moisture-sensor/docs/wiring-review-2026-09-09/layers/nrf-moisture-sensor-B_Cu.png

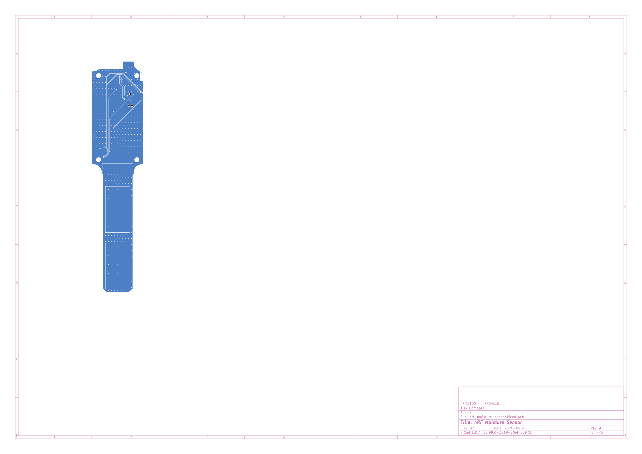
docs/wiring-review-2026-09-09/layers/nrf-moisture-sensor-B_Cu.png
