alxgmpr/moisture-sensor/docs/wiring-review-2026-09-09/layers/nrf-moisture-sensor-F_Cu.png

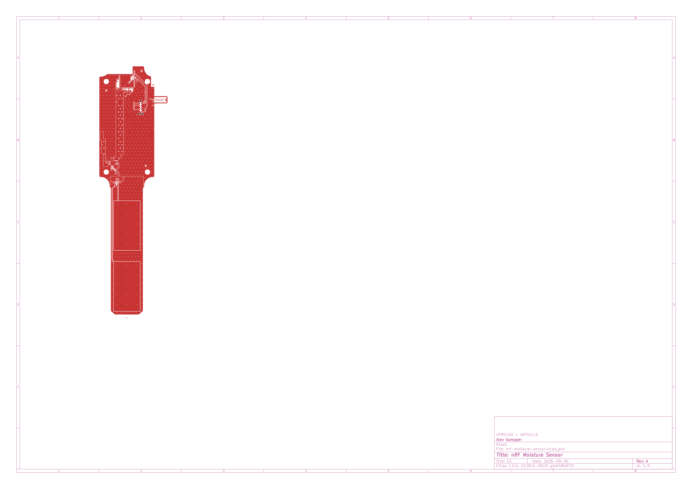
docs/wiring-review-2026-09-09/layers/nrf-moisture-sensor-F_Cu.png
