alxgmpr/moisture-sensor/docs/wiring-review-2026-09-09/power.png

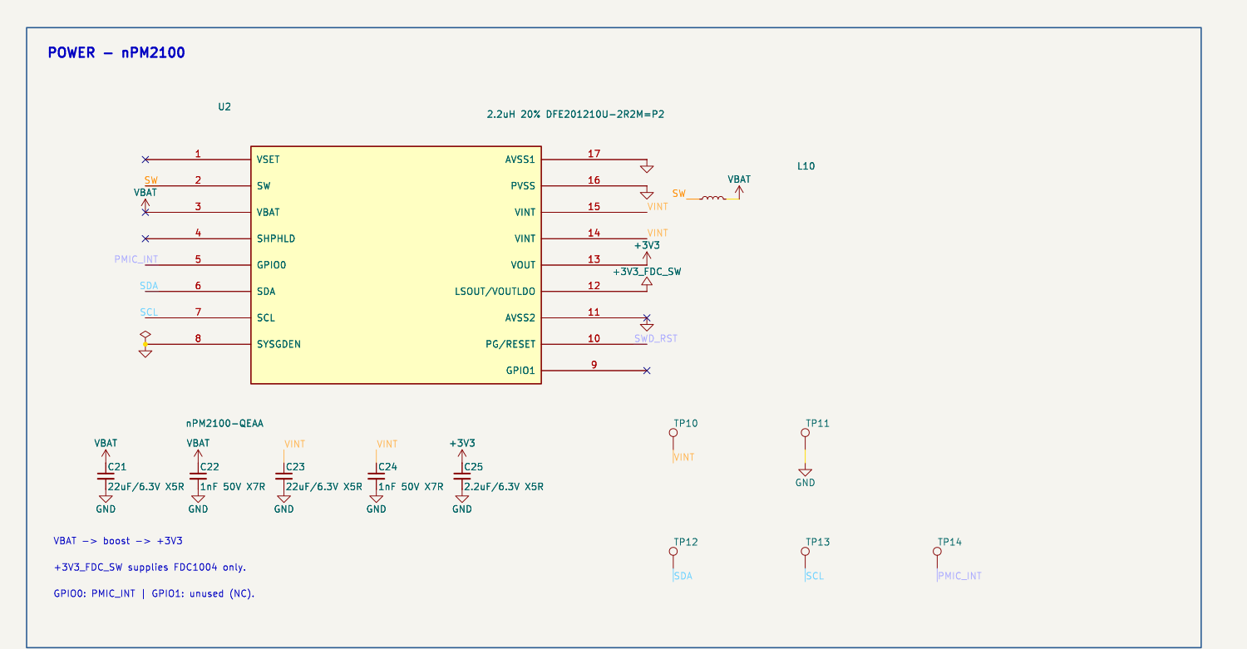
docs/wiring-review-2026-09-09/power.png
