alxgmpr/moisture-sensor/docs/wiring-review-2026-09-09/protection.png

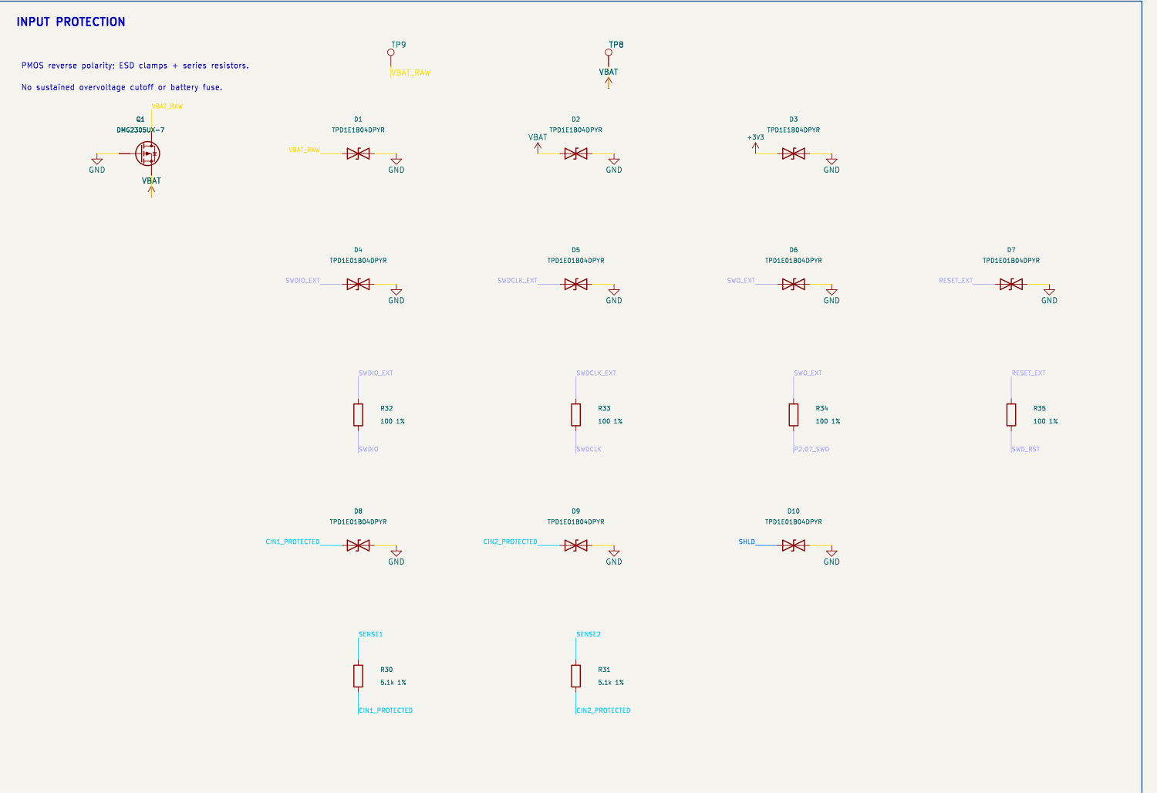
docs/wiring-review-2026-09-09/protection.png
