alxgmpr/moisture-sensor/docs/component-review-2026-09-05/c21-characteristics.png

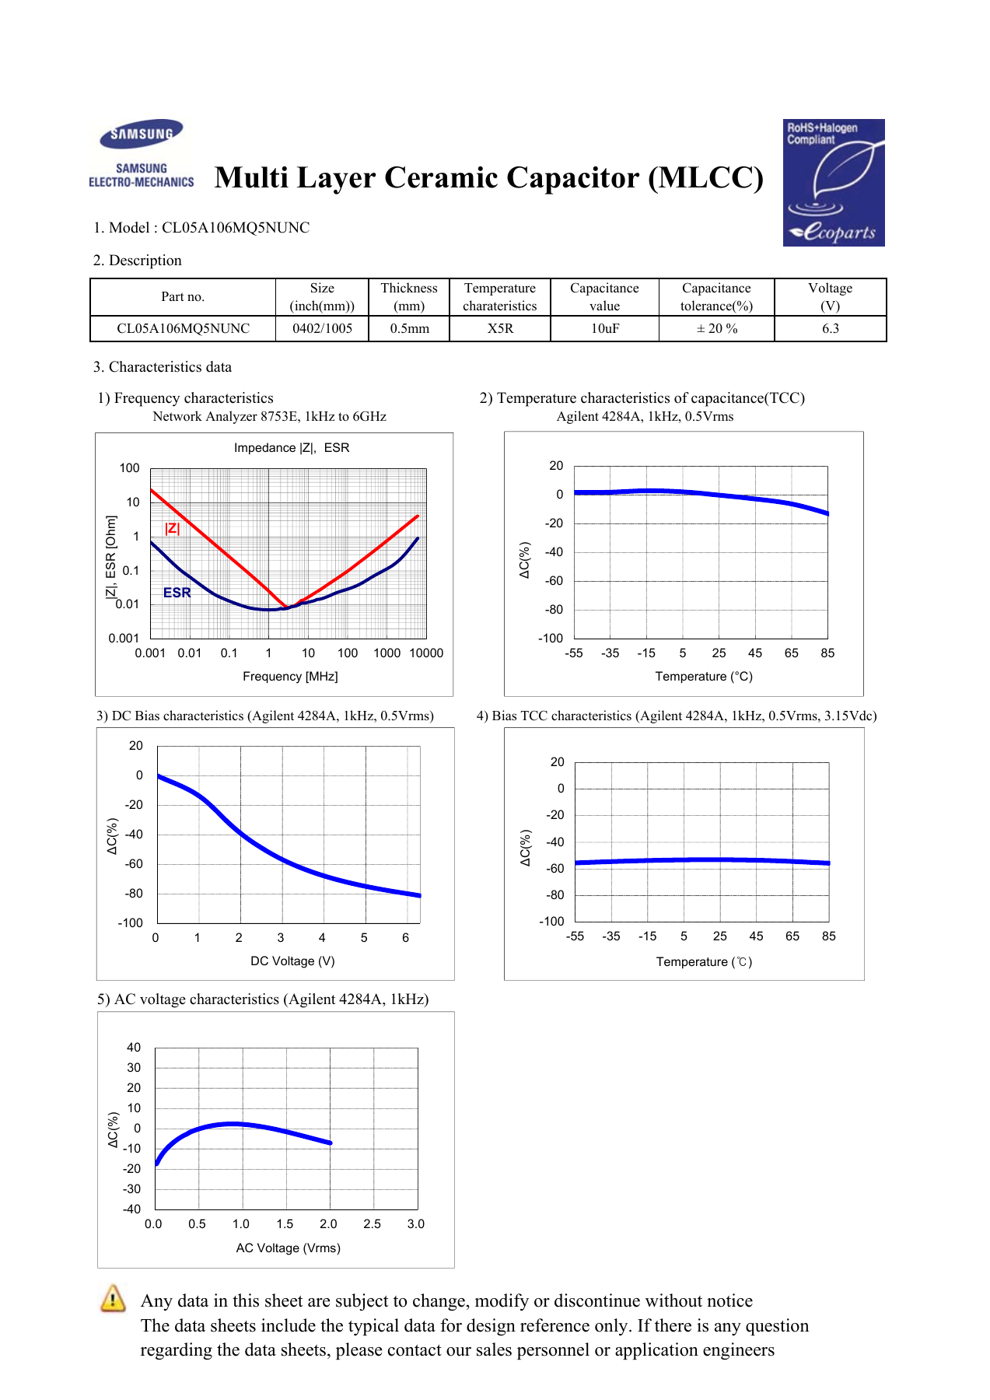
docs/component-review-2026-09-05/c21-characteristics.png
