alxgmpr/moisture-sensor/docs/testpoints-2026-09-07/front-head.png

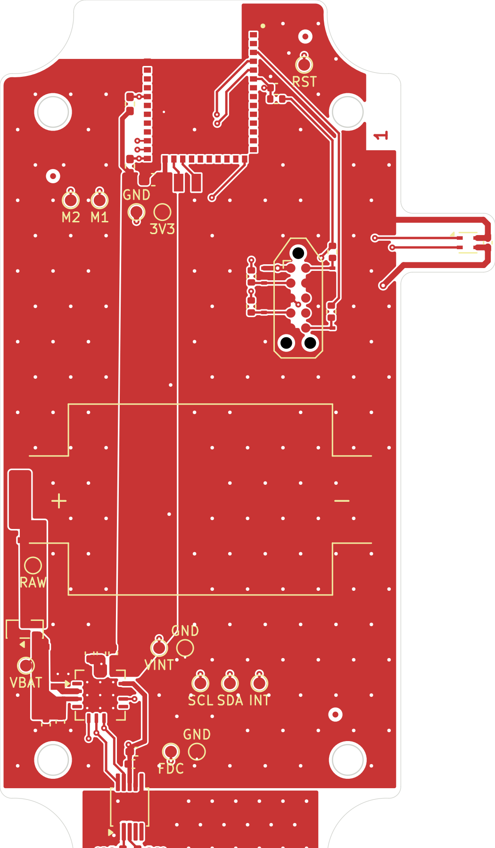
docs/testpoints-2026-09-07/front-head.png
