alxgmpr/moisture-sensor/docs/testpoints-2026-09-07/inner-head.png

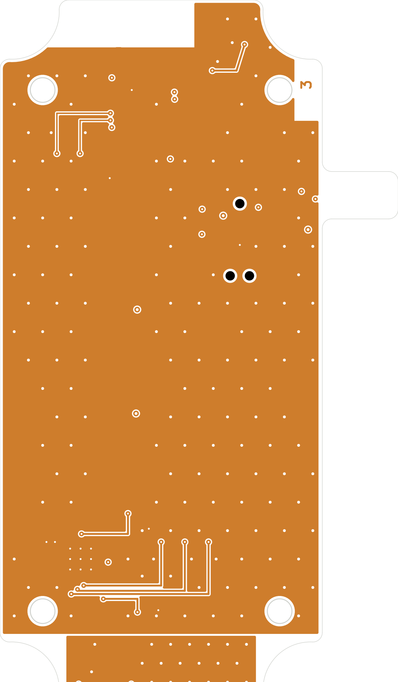
docs/testpoints-2026-09-07/inner-head.png
