alxgmpr/moisture-sensor/docs/footprint-standardization-2026-09-09/debug-3d.png

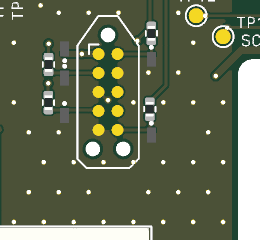
docs/footprint-standardization-2026-09-09/debug-3d.png
