alxgmpr/moisture-sensor/docs/protection/layout-debug.png

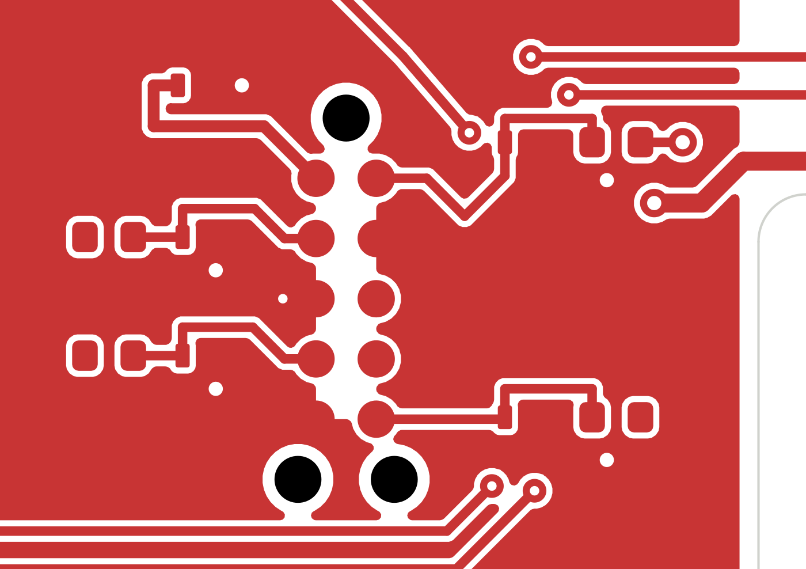
docs/protection/layout-debug.png
