alxgmpr/moisture-sensor/docs/schematic-review-2026-09-05/before/baseline.kicad_sch

## KiCad design docs/schematic-review-2026-09-05/before/baseline.kicad_sch (2026-09-06)

Schematic: baseline.kicad_sch

Parts:
BT1: CR2032-BS-6; BatteryHolder_LianXin_CR2032-BS-6; MPN CR2032-BS-6; LCSC C22363833
C3: 10uF/16V X6S; C_0603_1608Metric; MPN CL10X106MO8NRNC; LCSC C3039688
C13: 3.9pF C0G; C_0402_1005Metric; MPN 0402CG3R9C500NT; LCSC C1566
C21: 10uF/6.3V X5R; C_0402_1005Metric; MPN CL05A106MQ5NUNC; LCSC C15525
C22, C24: 1nF 50V X7R; C_0402_1005Metric; MPN 0402B102K500NT; LCSC C1523
C23: 22uF/6.3V X5R; C_0402_1005Metric; MPN GRM155R60J226ME11D; LCSC C415703
C25: 2.2uF/6.3V X5R; C_0402_1005Metric; MPN CL05A225MQ5NSNC; LCSC C12530
C26: 1uF 10V X7R; C_0402_1005Metric_Pad0.74x0.62mm_HandSolder; MPN GRM155Z71A105KE01D; LCSC C528974
C27, C28: 100nF 16V X7R; C_0402_1005Metric; MPN CL05B104KO5NNNC; LCSC C1525
D1, D2, D3: TPD1E1B04DPYR; TI_DPY0002A; MPN TPD1E1B04DPYR; LCSC C779408
D4, D5, D6, D7, D8, D9, D10: TPD1E01B04DPYR; TI_DPY0002A; MPN TPD1E01B04DPYR; LCSC C779389
FID1, FID2, FID3: Fiducial; Fiducial_0.5mm_Mask1mm
J4: SWD 10p 1.27mm; Tag-Connect_TC2050-IDC-NL_2x05_P1.27mm_Vertical
L10: 2.2uH 20% DFE201210U-2R2M=P2; IND_Murata_DFE201210U; MPN DFE201210U-2R2M=P2; LCSC C2049745
Q1: DMG2305UX-7; SOT-23; MPN DMG2305UX-7; LCSC C150470
R1: 1k 1%; R_0402_1005Metric; MPN 0402WGF1001TCE; LCSC C11702
R22, R23: 4.7k to +3V3; R_0402_1005Metric_Pad0.72x0.64mm_HandSolder; MPN 0402WGF4701TCE; LCSC C25900
R30, R31: 5.1k 1%; R_0402_1005Metric; MPN 0402WGF5101TCE; LCSC C25905
R32, R33, R34, R35: 100 1%; R_0402_1005Metric; MPN 0402WGF1000TCE; LCSC C25076
TP1: SENSE1; TestPoint_Pad_D1.0mm
TP2: SENSE2; TestPoint_Pad_D1.0mm
TP3: SHLD; TestPoint_Pad_D1.0mm
U1: 453-00001R BL54L15; Ezurio_BL54L15_453-00001; MPN 453-00001R; DigiKey 776-453-00001RCT-ND; not fitted
U2: nPM2100-QEAA; QFN-16-1EP_4x4mm_P0.65mm_EP2.7x2.7mm_ThermalVias; MPN NPM2100-QEAA-R7; LCSC C46968654
U3: FDC1004; MSOP-10_3x3mm_P0.5mm; MPN FDC1004DGSR; LCSC C2865994
U4: SHT45-AD1F; Sensirion_DFN-4_1.5x1.5mm_P0.8mm_SHT4x_NoCentralPad; MPN SHT45-AD1F-R2; LCSC C5360602
X1: CM8V-T1A 32.768kHz CL=7pF 20ppm; XTAL_CM8V-T1A_2012; MPN CM8V-T1A-32.768KHZ-7PF-20PPM-TA-QC; LCSC C5136974

Connections:
+3V3: C3.1, C25.1, C27.1, D3.1 (A1), J4.1, R22.1, R23.1, U1.26 (VDD_nRF), U2.13 (VOUT), U4.3 (VDD)
+3V3_FDC_SW: C26.1, C28.1, U2.12 (LSOUT/VOUTLDO), U3.8 (VDD)
CIN1_PROTECTED: R30.2, U3.2 (CIN1)
CIN2_PROTECTED: R31.2, U3.3 (CIN2)
GND: BT1.2 (-), C3.2, C13.2, C21.2, C22.2, C23.2, C24.2, C25.2, C26.2, C27.2, C28.2, D1.2 (A2), D2.2 (A2), D3.2 (A2), D4.2 (A2), D5.2 (A2), D6.2 (A2), D7.2 (A2), D8.2 (A2), D9.2 (A2), D10.2 (A2), J4.3, J4.5, J4.9, Q1.1 (G), U1.1 (GND), U1.16 (GND), U1.27 (GND), U1.39 (GND), U2.8 (SYSGDEN), U2.11 (AVSS2), U2.16 (PVSS), U2.17 (AVSS1), U3.7 (GND), U4.4 (VSS)
NRESET: C13.1, R1.1, U1.7 (nRESET)
P2.07_SWO: R34.2, U1.4 (P2.07/SWO)
PMIC_INT: U1.17 (P0.00), U2.5 (GPIO0)
RESET_EXT: D7.1 (A1), J4.10, R35.1
SCL: R23.2, U1.35 (P1.11), U2.7 (SCL), U3.9 (SCL), U4.2 (SCL)
SDA: R22.2, U1.28 (P1.10), U2.6 (SDA), U3.10 (SDA), U4.1 (SDA)
SENSE1: D8.1 (A1), R30.1, TP1.1
SENSE2: D9.1 (A1), R31.1, TP2.1
SHLD: D10.1 (A1), TP3.1, U3.1 (SHLD1), U3.6 (SHLD2)
SW: L10.1, U2.2 (SW)
SWDCLK: R33.2, U1.6 (SWDCLK)
SWDCLK_EXT: D5.1 (A1), J4.4, R33.1
SWDIO: R32.2, U1.5 (SWDIO)
SWDIO_EXT: D4.1 (A1), J4.2, R32.1
SWD_RST: R1.2, R35.2, U2.10 (PG/RESET)
SWO_EXT: D6.1 (A1), J4.6, R34.1
VBAT: C21.1, C22.1, D2.1 (A1), L10.2, Q1.2 (S), U2.3 (VBAT)
VBAT_RAW: BT1.1 (+), D1.1 (A1), Q1.3 (D)
VINT: C23.1, C24.1, U2.14 (VINT), U2.15 (VINT)
XL1: U1.25 (P1.00/XL1), X1.1
XL2: U1.24 (P1.01/XL2), X1.2

Notes on the sheet:
CR2032 BATTERY (NO CHARGING)
External: C3 10uF mandatory; X1 retained for timed System OFF wake.
XL1 = pad 25; XL2 = pad 24. Internal LFXO load bank; tune on hardware.
EXTERNAL 32.768 kHz
PMIC - nPM2100 (battery power / switched FDC rail)
MCU - Ezurio BL54L15
453-00001R PCB-antenna module. U1 DNP = JLC stage only; HAND FIT in product.
SENSE FRONT END - FDC1004
INPUT PROTECTION: PMOS reverse battery; ESD clamps + series isolation. No sustained overvoltage cutoff or battery fuse. Prototype ESD / leakage / sensing qualification required.
MODULE SUPPORT
SWD
C3 is 0603, 10uF/16V X6S. Verify VDD ripple <=10mV during radio.
Internal: 32 MHz crystal, DCDC support and RF matching/antenna.
